henkjannl/RoomThermostat/05 Software/Roomthermostat V2/Roomthermostat V2.0/design/architecture.ods

# | File | Module | Functionality | Called by | V1 | V2 | V3 | V4 | V5 | V6 | Include list
a | constants |  | Global constants |  | basic | basic | basic | basic | basic | basic | #include "a_constants.h"
b | interfaces |  | Datatypes for interfaces between objects |  | basic | basic | basic | basic | basic | basic | #include "b_interfaces.h"
c | logger | Logger |  |  | none | none | none | none | none | none | #include "c_logger.h"
d | boiler | Boiler | Sends requested water temperature Requests boiler status | MenuUnit and MenuTelegram Main loop for boiler status Locking mechanism with Buttons | stub | stub | stub | stub | stub | stub | #include "d_boiler.h"
e | roomtemp | RoomTemp | Measures roomtemperature |  | stub | stub | stub | stub | stub | stub | #include "e_roomtemp.h"
f | telegram | Telegram | Telegram connection | Main loop | none | none | none | none | none | none | #include "f_telegram.h"
g | button | Buttons | Polls each of the 3 buttons | Timer interrupt Locking mechanism with OpenTherm | full | full | full | full | full | full | #include "g_button.h"
h | display | Display | Displays latest status of bolier and menu | MenuUnit and OpenTherm | stub | basic | basic | basic | basic | basic | #include "h_display.h"
i | jpeg | JPEG | Library to display images | Display | full | full | full | full | full | full | #include "i_jpeg.h"
j | storage | Storage | Stores and retrieves program from non volatile memory |  | none | none | none | none | none | none | #include "j_storage.h"
k | wifi | WiFi | WiFi connection | Main loop | stub | stub | stub | stub | stub | stub | #include "k_wifi.h"
l | time | Time | Real time clock | Main loop | stub | stub | stub | stub | stub | stub | #include "l_time.h"
m | menu_telegram | MenuTelegram | Manages menu state for each Telegram user | Telegram | none | none | none | none | none | none | #include "m_menu_telegram.h"
n | menu_unit | MenuUnit | Manages menu state for the hardware unit | Buttons | basic | basic | basic | basic | basic | basic | #include "n_menu_unit.h"
o | controller | Controller | Temperature controller including - thermostat program - PID controller for boiler temperature | Main loop | basic | basic | basic | basic | basic | basic | #include "o_controller.h"
