henkjannl/RoomThermostat/02 User interface/GUI.jpg

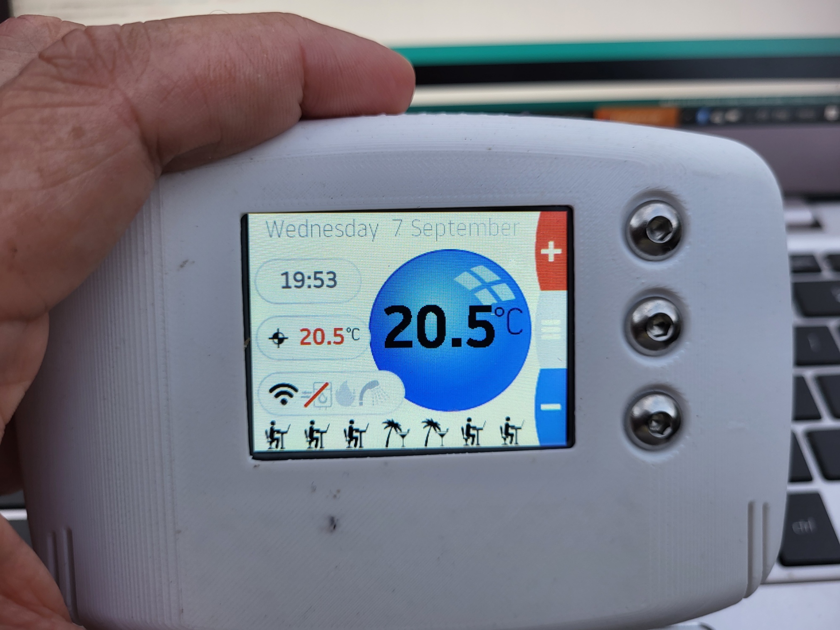
02 User interface/GUI.jpg
