henkjannl/RoomThermostat/02 User interface/photo.png

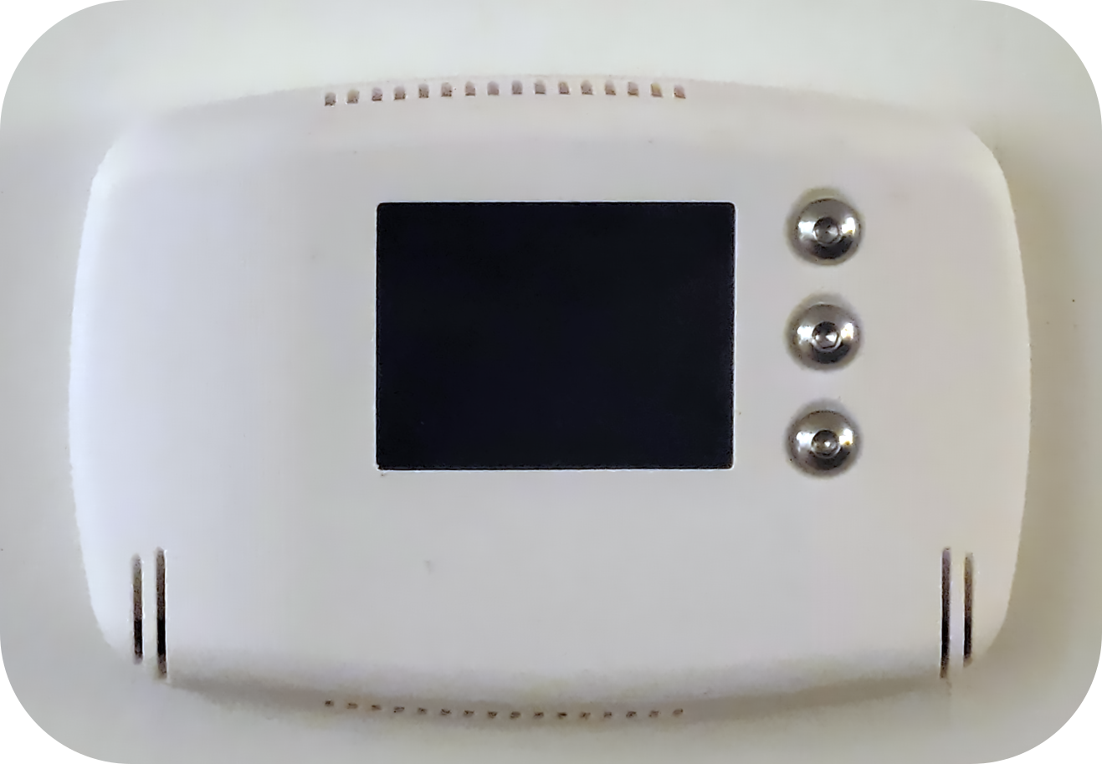
02 User interface/photo.png
