henkjannl/RoomThermostat/02 User interface/Telegram menu.png

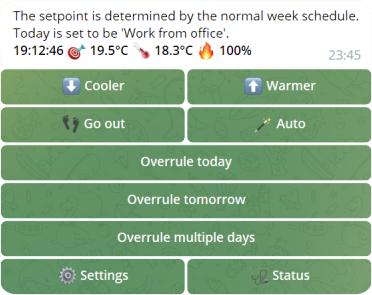
02 User interface/Telegram menu.png
