henkjannl/RoomThermostat/04 Electrical/Redesign PCB 3.0/20250117_201235.jpg

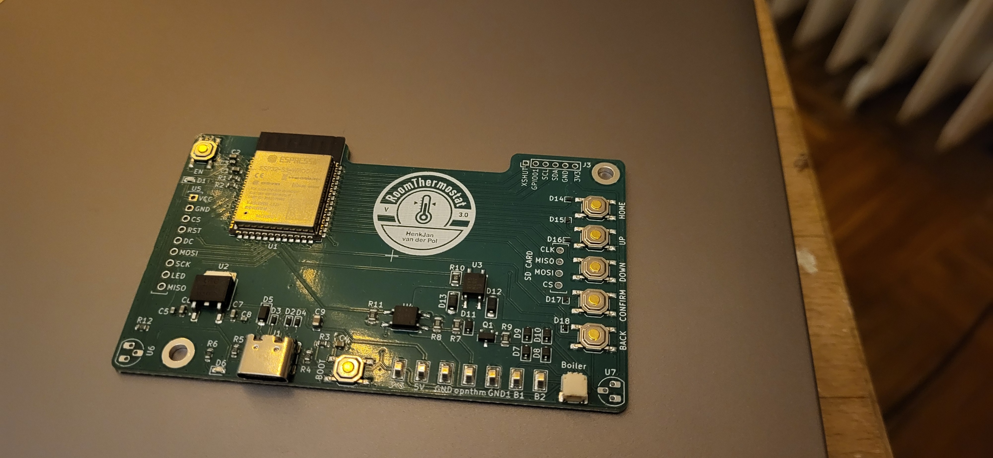
04 Electrical/Redesign PCB 3.0/20250117_201235.jpg
