henkjannl/RoomThermostat/04 Electrical/Redesign PCB 3.0/Interface board example project/Background info/Reverse engineering - case 4.png

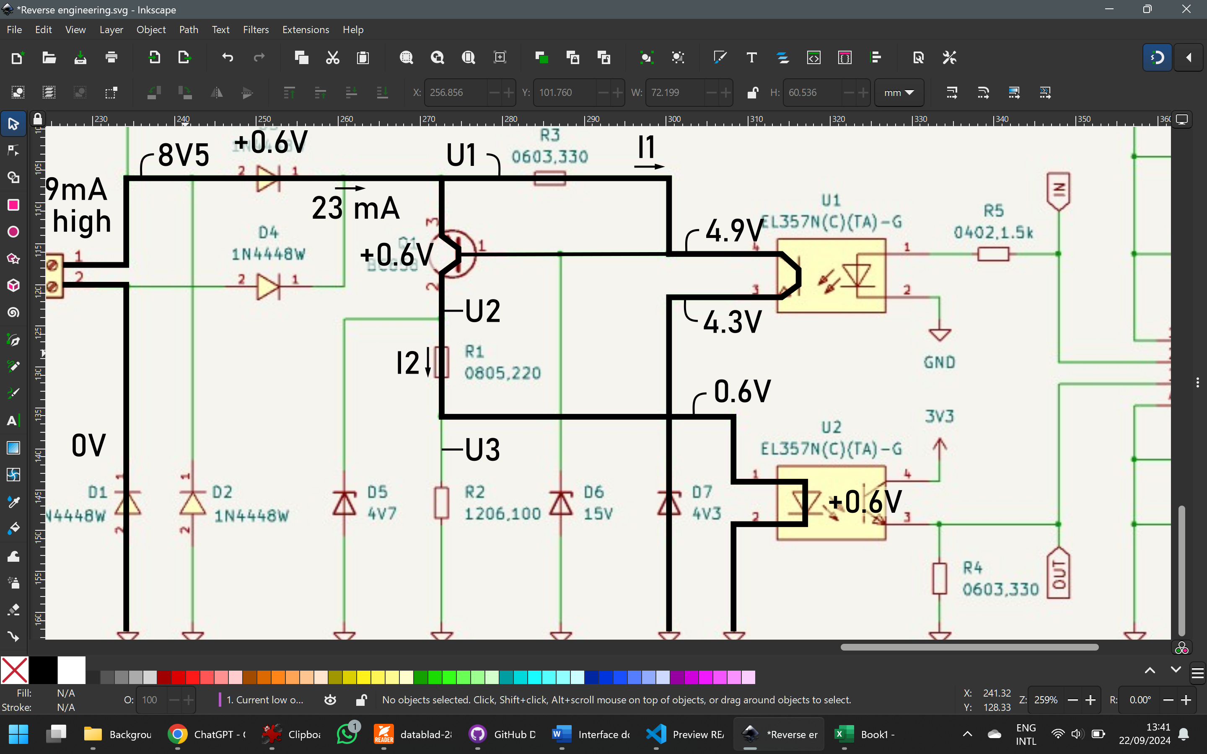
04 Electrical/Redesign PCB 3.0/Interface board example project/Background info/Reverse engineering - case 4.png
