henkjannl/RoomThermostat/04 Electrical/Redesign PCB 3.0/Photos DIYless/01.jpg

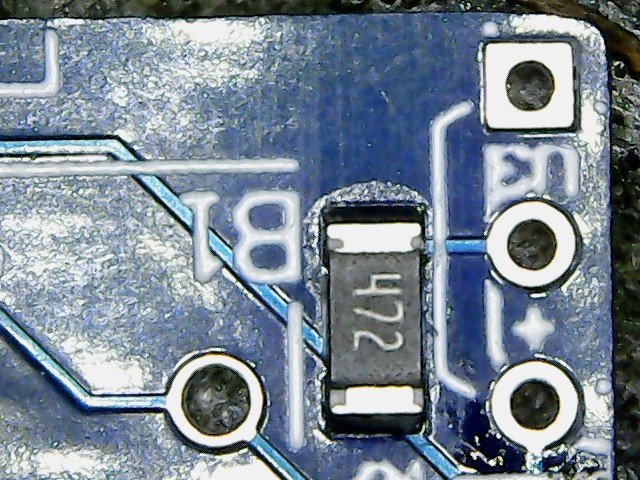
04 Electrical/Redesign PCB 3.0/Photos DIYless/01.jpg
