henkjannl/RoomThermostat/04 Electrical/Redesign PCB 3.0/Photos DIYless/09.jpg

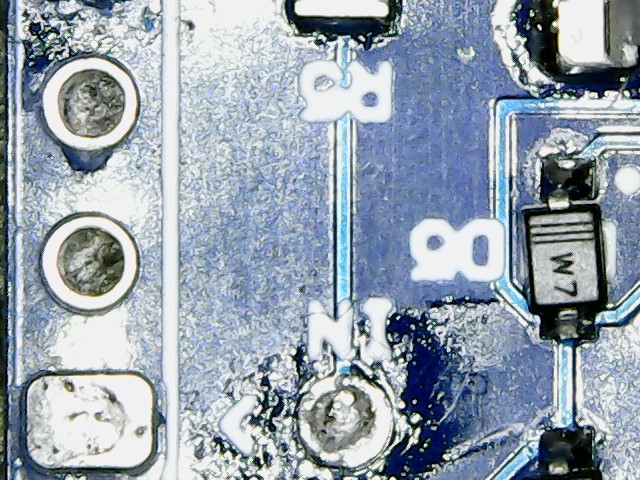
04 Electrical/Redesign PCB 3.0/Photos DIYless/09.jpg
