henkjannl/RoomThermostat/04 Electrical/Redesign PCB 3.0/Photos DIYless/17.jpg

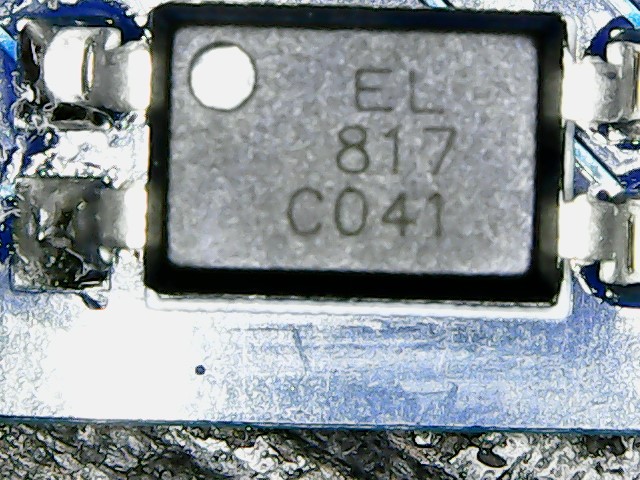
04 Electrical/Redesign PCB 3.0/Photos DIYless/17.jpg
