henkjannl/RoomThermostat/04 Electrical/Redesign PCB 3.0/Photos DIYless/18.jpg

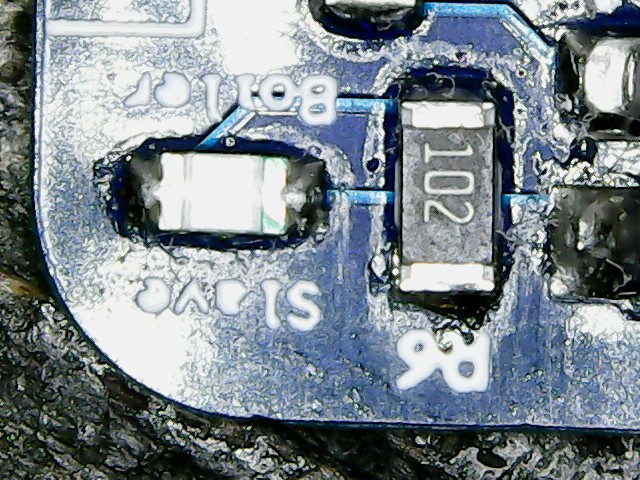
04 Electrical/Redesign PCB 3.0/Photos DIYless/18.jpg
