henkjannl/RoomThermostat/06 Logdata/Multiple day log.png

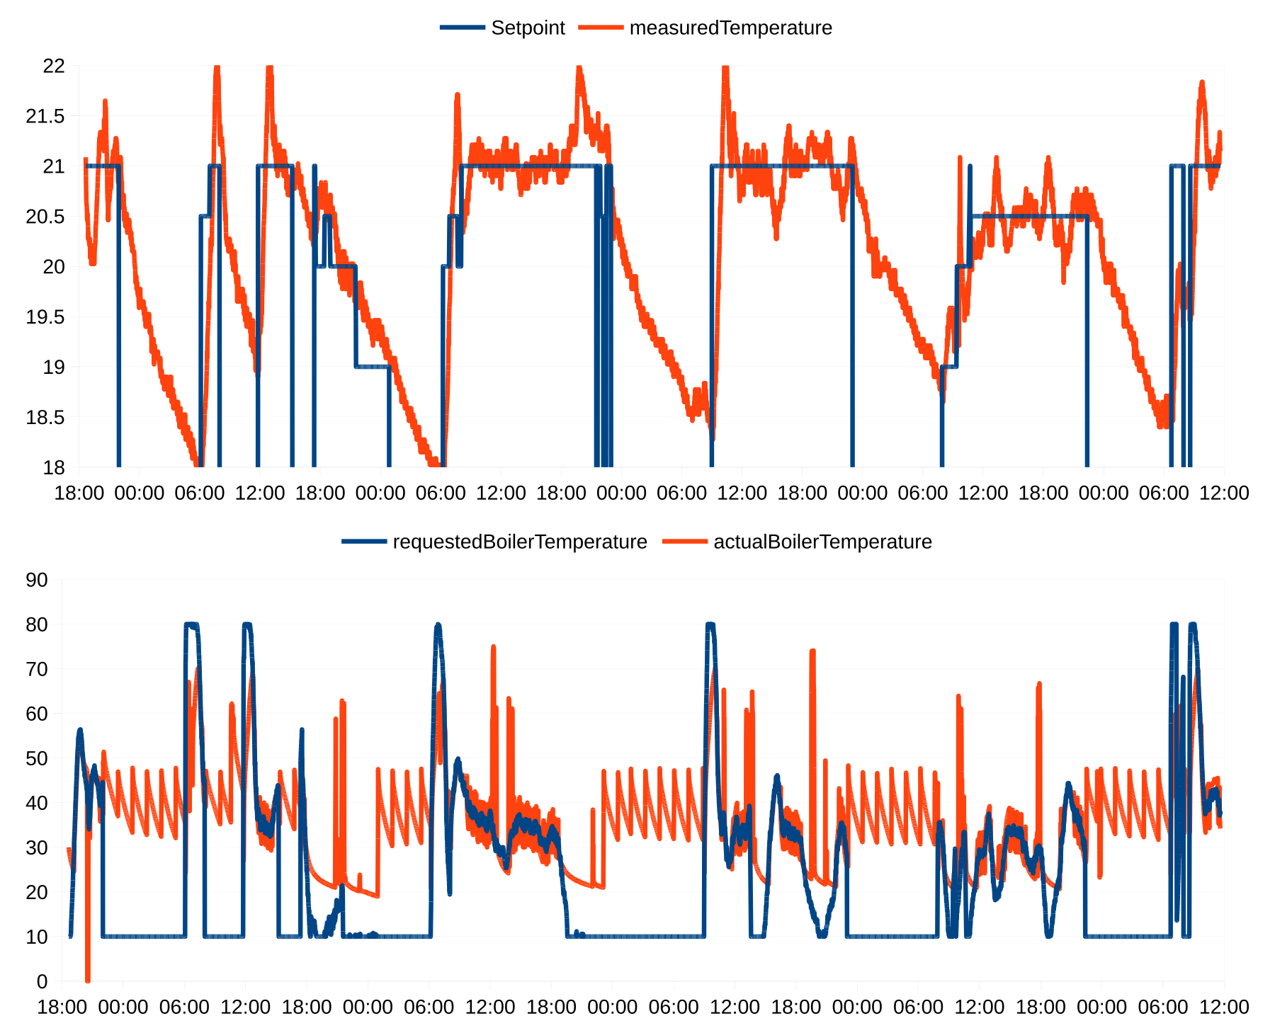
06 Logdata/Multiple day log.png
