henkjannl/RoomThermostat/07 Readonly/DIYless opentherm shield/Master Opentherm Shield 2.png

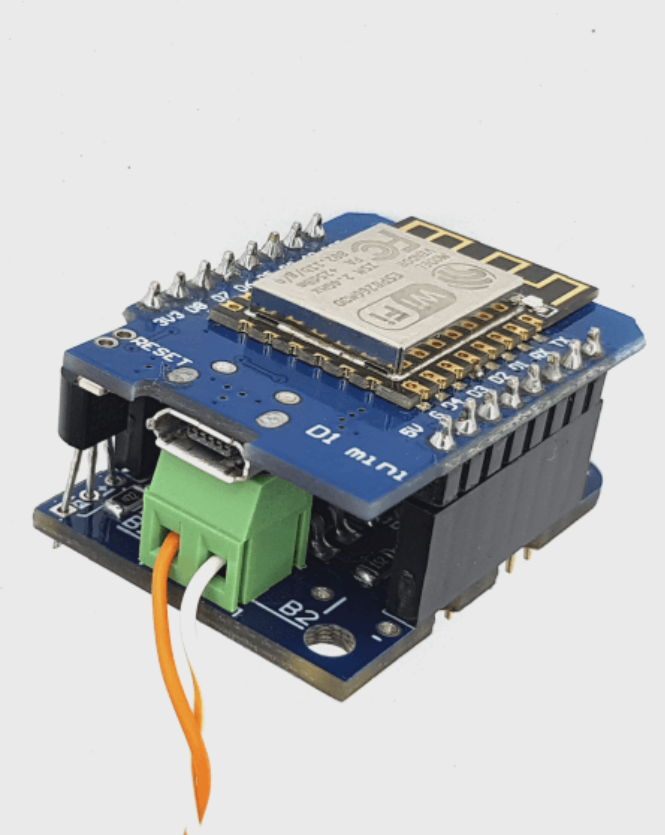
07 Readonly/DIYless opentherm shield/Master Opentherm Shield 2.png
