henkjannl/RoomThermostat/07 Readonly/DIYless opentherm shield/Master Opentherm Shield 3.png

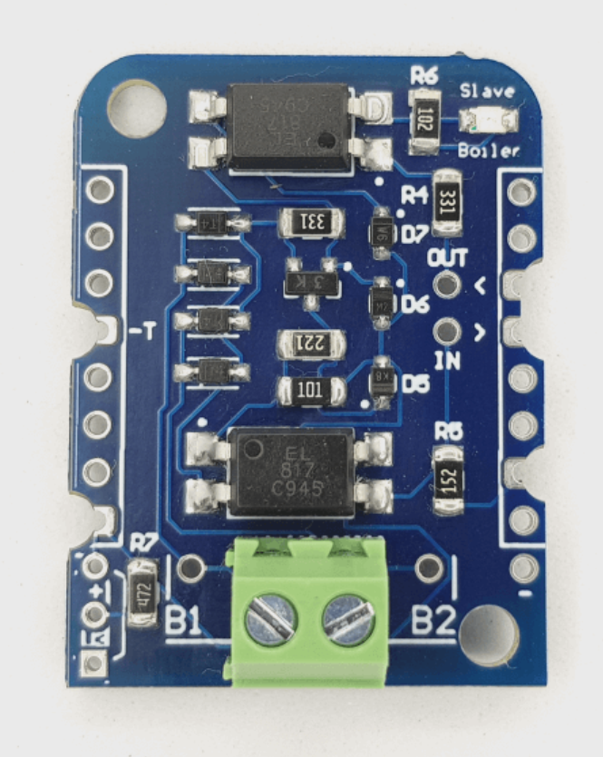
07 Readonly/DIYless opentherm shield/Master Opentherm Shield 3.png
