henkjannl/RoomThermostat/07 Readonly/DIYless opentherm shield/Master Opentherm Shield 4.png

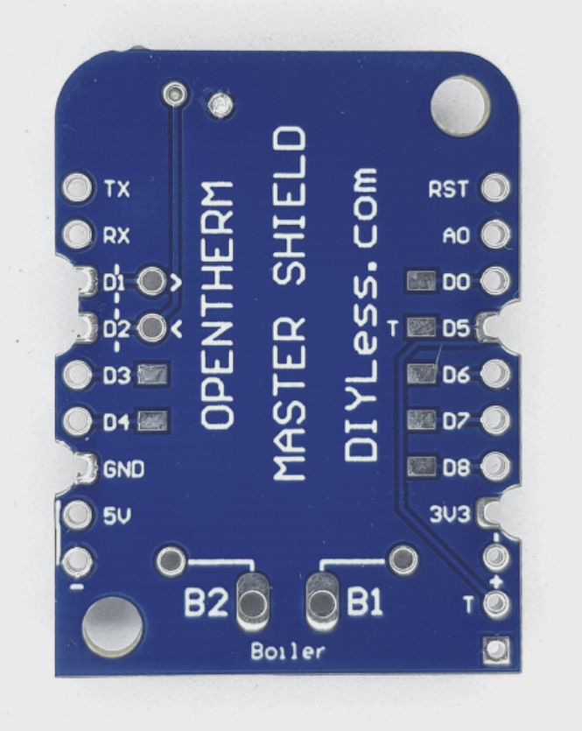
07 Readonly/DIYless opentherm shield/Master Opentherm Shield 4.png
