henkjannl/RoomThermostat/07 Readonly/DIYless opentherm shield/Schematic.png

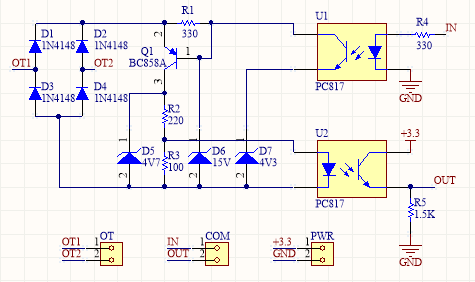
07 Readonly/DIYless opentherm shield/Schematic.png
