henkjannl/RoomThermostat/04 Electrical/Redesign PCB 3.0/Interface board example project/Background info/checklist.xlsx

Sheet: bom
New schematic | Original schematic | Original value | New value | LCSC Part # | Original description |  | Conrad Part No | Part subtype? | Current? | Orientation schematic? | Orientation board? | Footprint? | Datasheet | Footprint
D1 | D5 | 1N4148 | 1N4148WS_T4 | C2128 | Diode | Diode | 162280-89 |  |  |  |  |  | https://item.szlcsc.com/295156.html | SOD-323_L1.8-W1.3-LS2.5-RD
D2 | D6 | 1N4148 | 1N4148WS_T4 | C2128 | Diode | Diode | 162280-89 |  |  |  |  |  | https://item.szlcsc.com/295156.html | SOD-323_L1.8-W1.3-LS2.5-RD
D3 | D8 | 1N4148 | 1N4148WS_T4 | C2128 | Diode | Diode | 162280-89 |  |  |  |  |  | https://item.szlcsc.com/295156.html | SOD-323_L1.8-W1.3-LS2.5-RD
D4 | D7 | 1N4148 | 1N4148WS_T4 | C2128 | Diode | Diode | 162280-89 |  |  |  |  |  | https://item.szlcsc.com/295156.html | SOD-323_L1.8-W1.3-LS2.5-RD
D5 | D9 | 4V7 | 4V7 | C353517 | Zener Diode | Zener diode | 180084-89 |  |  |  |  |  | ~ | SOD-323_L1.8-W1.3-LS2.5-RD
D6 | D10 | 15V | 15V | C2104 | Zener Diode | Zener diode | 180203-89 |  |  |  |  |  | ~ | SOD-123_L2.7-W1.6-LS3.7-RD-1
D7 | D11 | 4V3 | 4V3 | C726993 | Zener Diode | Zener diode | 180076-89 |  |  |  |  |  | ~ | SOD-123_L2.7-W1.6-LS3.7-RD-1
J1 | - | - | Boiler | C395849 | Generic screw terminal, single row, 01x02, script generated (kicad-library-utils/schlib/autogen/connector/) |  | - |  |  |  |  |  | ~ | TerminalBlock_RND:TerminalBlock_RND_205-00001_1x02_P5.00mm_Horizontal
J2 | - | - | Screw_Terminal_01x04 | C557656 | Generic screw terminal, single row, 01x04, script generated (kicad-library-utils/schlib/autogen/connector/) |  | - |  |  |  |  |  | ~ | TerminalBlock_4Ucon:TerminalBlock_4Ucon_1x04_P3.50mm_Vertical
Q1 | Q1 | BC558A | BC858 | C549539 | PNP Transistor | PNP transistor, base/collector/emitter | 1262971-89 |  |  |  |  |  | ~ | SOT-23-5_L3.0-W1.7-P0.95-LS2.8-BL
R1 | R3 | 220 | 805220 | C17557 | 1/4 Watt 5% Resistor | 1% 1 8W Thick Film Resistors 150V 100ppm -55 155 220 0805 Chip Resistor - Surface Mount ROHS | 1417693-89 |  |  |  |  |  | https://datasheet.lcsc.com/lcsc/2110251830_UNI-ROYAL-Uniroyal-Elec-0805W8F2200T5E_C17557.pdf | 0805_2012Metric
R2 | R2 | 100 | 1206100 | C17901 | 1/4 Watt 5% Resistor |  | 1417639-89 |  |  |  |  |  |  | 1206_3216Metric
R3 | R1 | 330 | 603330 | C23138 | 1/4 Watt 5% Resistor | 1% 1 4W Thick Film Resistors 200V 100ppm -55 155 100 1206 Chip Resistor - Surface Mount ROHS | 1417730-89 |  |  |  |  |  | https://datasheet.lcsc.com/lcsc/2110252130_UNI-ROYAL-Uniroyal-Elec-0603WAF3300T5E_C23138.pdf | 0603_1608Metric
R4 | R4 | 330 | 603330 | C23138 | 1/4 Watt 5% Resistor | 1% 1 10W Thick Film Resistors 75V 100ppm -55 155 330 0603 Chip Resistor - Surface Mount ROHS | 1417730-89 |  |  |  |  |  | https://datasheet.lcsc.com/lcsc/2110252130_UNI-ROYAL-Uniroyal-Elec-0603WAF3300T5E_C23138.pdf | 0603_1608Metric
R5 | R8 | 1k2 | 0402,1.5k | C25867 | 1/4 Watt 5% Resistor | 1% 1 10W Thick Film Resistors 75V 100ppm -55 155 330 0603 Chip Resistor - Surface Mount ROHS | 1417712-89 |  |  |  |  |  |  | 0402_1005Metric
U1 | OK1A | PC827 | EL357N(C)(TA)-G | C29981 | Dual opto-coupler |  | 140235-89 |  |  |  |  |  | https://item.szlcsc.com/7114.html | OPTO-SMD-4_L4.4-W4.1-P2.54-LS7.0-TL
U2 | OK1B | PC827 | EL357N(C)(TA)-G | C29981 | Dual opto-coupler |  | 140235-89 |  |  |  |  |  | https://item.szlcsc.com/7114.html | OPTO-SMD-4_L4.4-W4.1-P2.54-LS7.0-TL
D5 |  |  | 4V7 |  |  |  |  |  |  |  |  |  | ~ | footprint:SOD-323_L1.8-W1.3-LS2.5-RD
D6 |  |  | 15V |  |  |  |  |  |  |  |  |  | ~ | footprint:SOD-123_L2.7-W1.6-LS3.7-RD-1
D7 |  |  | 4V3 |  |  |  |  |  |  |  |  |  | ~ | footprint:SOD-123_L2.7-W1.6-LS3.7-RD-1
J1 |  |  | Boiler
J2 |  |  | Screw_Terminal_01x04
Q1 |  |  | BC858 |  |  |  |  |  |  |  |  |  | ~ | footprint:SOT-23-3_L2.9-W1.3-P1.90-LS2.4-BR
R1 |  |  | 805220 |  |  |  |  |  |  |  |  |  | https://datasheet.lcsc.com/lcsc/2110251830_UNI-ROYAL-Uniroyal-Elec-0805W8F2200T5E_C17557.pdf | footprint:0805_2012Metric
R2 |  |  | 1206100 |  |  |  |  |  |  |  |  |  | https://datasheet.lcsc.com/lcsc/2110251930_UNI-ROYAL-Uniroyal-Elec-1206W4F1000T5E_C17901.pdf | footprint:1206_3216Metric
R3,R4 |  |  | 603330 |  |  |  |  |  |  |  |  |  | https://datasheet.lcsc.com/lcsc/2110252130_UNI-ROYAL-Uniroyal-Elec-0603WAF3300T5E_C23138.pdf | footprint:0603_1608Metric
R5 |  |  | 0402,1.5k |  |  | 1% 1 16W Thick Film Resistors 50V 100ppm -55 155 1 5k 0402 Chip Resistor - Surface Mount ROHS |  |  |  |  |  |  | https://datasheet.lcsc.com/lcsc/2110260030_UNI-ROYAL-Uniroyal-Elec-0402WGF1501TCE_C25867.pdf | footprint:0402_1005Metric
U1,U2 |  |  | EL357N(C)(TA)-G |  |  |  |  |  |  |  |  |  |  | footprint:OPTO-SMD-4_L4.4-W4.1-P2.54-LS7.0-TL

Sheet: Sheet1
Qty | Description | Value | Reference | Conrad Part No
1 | PIC processor | PIC16F88P | IC1 | 165233-89
1 | RS232 interfacemodule | MAX232 | IC2 | 152281-89
1 | Voltage Regulator TO220 | MC7805CT | IC3 | 175030-89
1 | Dual opto-coupler | PC827 | OK1 | 140235-89
4 | PNP Transistor | BC558A | Q1, Q2, Q3, Q5 | 1262971-89
1 | NPN Transistor | BC547B | Q4 | 1262957-89
1 | Electrolytic Capacitor, Radial 63V | 220µF | C1 | 445902-89
1 | Electrolytic Capacitor, Radial 16V | 100µF | C2 | 445928-89
4 | Electrolytic Capacitor, Radial 50V | 1µF | C3, C4, C5, C6 | 445724-89
4 | Diode | 1N4004 | D1, D2, D3, D4 | 162248-89
4 | Diode | 1N4148 | D5, D6, D7, D8 | 162280-89
1 | Zener Diode | 4V7 | D9 | 180084-89
1 | Zener Diode | 15V | D10 | 180203-89
1 | Zener Diode | 4V3 | D11 | 180076-89
1 | 1/4 Watt 5% Resistor | 39 | R12 | 1417702-89
2 | 1/4 Watt 5% Resistor | 100 | R2, R11 | 1417639-89
1 | 1/4 Watt 5% Resistor | 220 | R3 | 1417693-89
2 | 1/4 Watt 5% Resistor | 330 | R1, R4 | 1417730-89
1 | 1/4 Watt 5% Resistor | 1k2 | R8 | 1417712-89 | 1k2 or 1k5?
2 | 1/4 Watt 5% Resistor | 4k7 | R6, R9 | 1417695-89
1 | 1/4 Watt 5% Resistor | 15k | R10 | 1417711-89
2 | 1/4 Watt 5% Resistor | 33k | R5, R7 | 1417647-89
1* | Transformer EI30 | 15V 1.2VA | TR1 | 710691-89
1 | Header | 10 pin | SV1 | 741648-89
3 | Screw Clamp | 2 pin | X1, X2, X3 | 731091-89

Sheet: NewKicadProject
Reference | Value | LCSC | Datasheet | Footprint | Qty | DNP | Description
D1,D2,D3,D4 | 1N4148WS_T4 | C2128 | https://item.szlcsc.com/295156.html | footprint:SOD-323_L1.8-W1.3-LS2.5-RD | 4
D5 | 4V7 | C353517 | ~ | footprint:SOD-323_L1.8-W1.3-LS2.5-RD | 1 |  | Zener diode
D6 | 15V | C2104 | ~ | footprint:SOD-123_L2.7-W1.6-LS3.7-RD-1 | 1 |  | Zener diode
D7 | 4V3 | C726993 | ~ | footprint:SOD-123_L2.7-W1.6-LS3.7-RD-1 | 1 |  | Zener diode
J1 | Boiler | C395849 | ~ | TerminalBlock_RND:TerminalBlock_RND_205-00001_1x02_P5.00mm_Horizontal | 1 |  | Generic screw terminal, single row, 01x02, script generated (kicad-library-utils/schlib/autogen/connector/)
J2 | Screw_Terminal_01x04 | C557656 | ~ | TerminalBlock_4Ucon:TerminalBlock_4Ucon_1x04_P3.50mm_Vertical | 1 |  | Generic screw terminal, single row, 01x04, script generated (kicad-library-utils/schlib/autogen/connector/)
Q1 | BC858 | C549539 | ~ | footprint:SOT-23-3_L2.9-W1.3-P1.90-LS2.4-BR | 1 |  | PNP transistor, base/collector/emitter
R1 | 805220 | C17557 | https://datasheet.lcsc.com/lcsc/2110251830_UNI-ROYAL-Uniroyal-Elec-0805W8F2200T5E_C17557.pdf | footprint:0805_2012Metric | 1 |  | 1% 1 8W Thick Film Resistors 150V 100ppm -55 155 220 0805 Chip Resistor - Surface Mount ROHS
R2,R3 | 603330 | C23138 | https://datasheet.lcsc.com/lcsc/2110252130_UNI-ROYAL-Uniroyal-Elec-0603WAF3300T5E_C23138.pdf | footprint:0603_1608Metric | 2 |  | 1% 1 10W Thick Film Resistors 75V 100ppm -55 155 330 0603 Chip Resistor - Surface Mount ROHS
R4 | 0402,1.5k | C25867 | https://datasheet.lcsc.com/lcsc/2110260030_UNI-ROYAL-Uniroyal-Elec-0402WGF1501TCE_C25867.pdf | footprint:0402_1005Metric | 1 |  | 1% 1 16W Thick Film Resistors 50V 100ppm -55 155 1 5k 0402 Chip Resistor - Surface Mount ROHS
R6 | 1206100 | C17901 | https://datasheet.lcsc.com/lcsc/2110251930_UNI-ROYAL-Uniroyal-Elec-1206W4F1000T5E_C17901.pdf | footprint:1206_3216Metric | 1 |  | 1% 1 4W Thick Film Resistors 200V 100ppm -55 155 100 1206 Chip Resistor - Surface Mount ROHS
U1,U2 | EL357N(C)(TA)-G | C29981 | https://item.szlcsc.com/7114.html | footprint:OPTO-SMD-4_L4.4-W4.1-P2.54-LS7.0-TL | 2
