henkjannl/RoomThermostat/05 Software/Tests/Test08_monitor_chromoterm/Monitoring the Honeywell.xlsx

Sheet: Sheet1
Max voltage | U1 | 18 | V |  | R2 |  | R1 | U2 | I | 2.668769716
Scaled down to | U2 | 2.4 | V |  | 10
 |  |  |  |  | 22
U2/R1=U1/(R1+R2) |  |  |  |  | 47
U2*R1+U2*R2=U1*R1 |  |  |  |  | 100 | 17.64705882 | 10 | 1.636363636 | 0.1636363636
(U2-U1)*R1=-U2*R2 |  |  |  |  | 150 | 26.47058824 | 22 | 2.302325581 | 0.1046511628
R2=(U1-U2)/U2*R1 |  |  |  |  | 200 | 35.29411765 | 22 | 1.783783784 | 0.08108108108
 |  |  |  |  | 220 | 38.82352941 | 22 | 1.636363636 | 0.07438016529
Resistor 1 | R1 | 330 | ohm |  | 270 | 47.64705882 | 47 | 2.668769716 | 0.05678233438
Resistor 2 | R2 | 2000 | ohm |  | 330 | 58.23529412 | 47 | 2.24403183 | 0.04774535809
 |  |  |  |  | 470 | 82.94117647 | 47 | 1.636363636 | 0.03481624758
 |  | U1 | U2 | readout | 510 | 90 | 47 | 1.518850987 | 0.03231597846
 |  | 18 | 2.549356223 | 3163.519313 | 680 | 120 | 100 | 2.307692308 | 0.02307692308
 |  | 16.9 | 2.393562232 | 2970.193133 | 1000 | 176.4705882 | 150 | 2.347826087 | 0.01565217391
 |  | 8.9 | 1.260515021 | 1564.184549 | 2000 | 352.9411765 | 330 | 2.549356223 | 0.007725321888
 |  | 6.3 | 0.8922746781 | 1107.23176 | 2200 | 388.2352941 | 330 | 2.347826087 | 0.007114624506
 |  | 0 | 0 | 0 | 3300 | 582.3529412 | 510 | 2.409448819 | 0.004724409449
 |  |  |  |  | 4700 | 829.4117647 | 680 | 2.275092937 | 0.003345724907
Readout scale |  | 0.00568986569 |  |  | 5100 | 900 | 680 | 2.117647059 | 0.003114186851
 |  |  |  |  | 6800 | 1200 | 1000 | 2.307692308 | 0.002307692308
 |  |  |  |  | 10000 | 1764.705882 | 1000 | 1.636363636 | 0.001636363636
 |  |  |  |  | 20000 | 3529.411765 | 3300 | 2.549356223 | 0.0007725321888
 |  |  |  |  | 47000 | 8294.117647 | 6800 | 2.275092937 | 0.0003345724907
 |  |  |  |  | 51000 | 9000 | 6800 | 2.117647059 | 0.0003114186851
 |  |  |  |  | 68000 | 12000 | 10000 | 2.307692308 | 0.0002307692308
 |  |  |  |  | 100000 | 17647.05882 | 10000 | 1.636363636 | 0.0001636363636
 |  |  |  |  | 220000 | 38823.52941 | 20000 | 1.5 | 7.5e-05
 |  |  |  |  | 300000 | 52941.17647 | 51000 | 2.615384615 | 5.128205128e-05
 |  |  |  |  | 470000 | 82941.17647 | 68000 | 2.275092937 | 3.345724907e-05
 |  |  |  |  | 680000 | 120000 | 100000 | 2.307692308 | 2.307692308e-05
 |  |  |  |  | 1000000 | 176470.5882 | 100000 | 1.636363636 | 1.636363636e-05

Sheet: Sheet2
217 | 4490
46
218
43
220
43
228
44
230
35
230
34
233
36
235
34
235
32
231
30
235
35
240
31
240
31
240
33
240
31
240
240

Sheet: Sheet3
Utotal | 18 | V
R2 | 2000 | ohm
R1 | 330 | ohm
Rtotal | 2330 | ohm
Itotal | 0.007725321888 | A
U1 | 2.549356223 | V
8.8
24.2
16.5
