henkjannl/RoomThermostat/04 Electrical/Redesign PCB 3.0/Interface board example project/Background info/Reverse engineering.xlsx

Sheet: Case 1
Case 1
Output | LOW
I1 | 0.009 | A
Value of U2 based on output
D6 | 15 | V
D7 | 4.3 | V
U2 | 15 | V
 |  |  |  |  |  |  | I2/I1 | U1 | U2 | U1-U2 | U3 | U4 | I4
Split I2/I3 |  |  |  |  |  |  |  | 15.0297 | 15 | 0.0297 | 4.7 | 1.46875 | 0.0146875
I2/I1 | 1% |  | I2+I3=I1 |  |  |  | 0% | 15 | 15 | 0 | 4.7 | 1.46875 | 0.0146875
I2 | 9e-05 | A | I2/I3=p |  |  |  | 5% | 15.1485 | 15 | 0.1485 | 4.7 | 1.46875 | 0.0146875
I3 | 0.00891 | A | I2=p*I3 |  |  |  | 10% | 15.297 | 15 | 0.297 | 4.7 | 1.46875 | 0.0146875
R3 | 330 | Ω | I2+I2/p=I1 |  |  |  | 15% | 15.4455 | 15 | 0.4455 | 4.7 | 1.46875 | 0.0146875
U1 | 15.0297 | V | I2=p*I1/(1+p) |  |  |  | 20% | 15.594 | 15 | 0.594 | 4.7 | 1.46875 | 0.0146875
 |  |  |  |  |  |  | 25% | 15.7425 | 15 | 0.7425 | 4.7 | 1.46875 | 0.0146875
U1-U2 | 0.0297 | V |  |  |  |  | 30% | 15.891 | 15 | 0.891 | 4.7 | 1.46875 | 0.0146875
Q1 will isolate |  |  |  |  |  |  | 35% | 16.0395 | 15 | 1.0395 | 4.7 | 1.46875 | 0.0146875
 |  |  |  |  |  |  | 40% | 16.188 | 15 | 1.188 | 4.7 | 1.46875 | 0.0146875
U3' | 14.4297 | V | Ignoring D5 |  |  |  | 45% | 16.3365 | 15 | 1.3365 | 4.7 | 1.46875 | 0.0146875
D5 | 4.7 | V |  |  |  |  | 50% | 16.485 | 15 | 1.485 | 4.7 | 1.46875 | 0.0146875
D5 will limit U3 |  |  |  |  |  |  | 55% | 16.6335 | 15 | 1.6335 | 4.7 | 1.46875 | 0.0146875
U3 | 4.7 | V |  |  |  |  | 60% | 16.782 | 15 | 1.782 | 4.7 | 1.46875 | 0.0146875
 |  |  |  |  |  |  | 65% | 16.9305 | 15 | 1.9305 | 4.7 | 1.46875 | 0.0146875
Ignoring Optocoupler: |  |  |  |  |  |  | 70% | 17.079 | 15 | 2.079 | 4.7 | 1.46875 | 0.0146875
R1 | 220 | Ω |  |  |  |  | 75% | 17.2275 | 15 | 2.2275 | 4.7 | 1.46875 | 0.0146875
R2 | 100 | Ω |  | U4 | 1.3 | V | 80% | 17.376 | 15 | 2.376 | 4.7 | 1.46875 | 0.0146875
I4 | 0.0146875 | A |  |  |  |  | 85% | 17.5245 | 15 | 2.5245 | 4.7 | 1.46875 | 0.0146875
U4 | 1.46875 | V |  |  |  |  | 90% | 17.673 | 15 | 2.673 | 4.7 | 1.46875 | 0.0146875
 |  |  |  |  |  |  | 95% | 17.8215 | 15 | 2.8215 | 4.7 | 1.46875 | 0.0146875
Opamp will limit U4 |  |  |  |  |  |  | 100% | 17.97 | 15 | 2.97 | 4.7 | 1.46875 | 0.0146875
U4 | 1.3 | V
I4 | 0.01545454545 | A |  |  |  |  | Average | 16.485 | 15 |  | 4.7 | 1.46875 | 0.0146875
I5 | -0.006544545455 | A
Recalculate I4 if I5<0
I4 | 0.00891 | A
U3 | 3.2602 | V
U1-U3 | 11.7695 | V

Sheet: Case 2
Case 2
Output | HIGH
I1 | 0.009 | A
Value of U2 based on output
D6 | 15 | V
D7 | 4.3 | V
U2 | 4.3 | V
 |  |  |  |  |  |  | I2/I1 | U1 | U2 | U3 | U4 | I4
Split I2/I3 |  |  |  |  |  |  |  | 4.3 | 3.7 | 3.28 | 1.3 | 0.0115625
I2/I1 | 0% |  | I2+I3=I1 |  |  |  | 0% | 4.3 | 3.7 | 3.28 | 1.3 | 0.0115625
I2 | 0 | A | I2/I3=p |  |  |  | 5% | 4.4485 | 3.8485 | 3.181 | 1.3 | 0.0120265625
I3 | 0.009 | A | I2=p*I3 |  |  |  | 10% | 4.597 | 3.997 | 3.082 | 1.3 | 0.012490625
R3 | 330 | Ω | I2=I1/(1+p) |  |  |  | 15% | 4.7455 | 4.1455 | 2.983 | 1.3 | 0.0129546875
U1 | 4.3 | V |  |  |  |  | 20% | 4.894 | 4.294 | 2.884 | 1.3 | 0.01341875
 |  |  |  |  |  |  | 25% | 5.0425 | 4.4425 | 2.785 | 1.3 | 0.0138828125
U1-U2 | 0 | V |  |  |  |  | 30% | 5.191 | 4.591 | 2.686 | 1.3 | 0.014346875
Q1 will isolate |  |  |  |  |  |  | 35% | 5.3395 | 4.7 | 2.587 | 1.3 | 0.0146875
 |  |  |  |  |  |  | 40% | 5.488 | 4.7 | 2.488 | 1.3 | 0.0146875
U3' | 3.7 | V | Ignoring D5 |  |  |  | 45% | 5.6365 | 4.7 | 2.389 | 1.3 | 0.0146875
D5 | 4.7 | V |  |  |  |  | 50% | 5.785 | 4.7 | 2.29 | 1.3 | 0.0146875
D5 will not limit U3 |  |  |  |  |  |  | 55% | 5.9335 | 4.7 | 2.191 | 1.3 | 0.0146875
U3 | 3.7 | V |  |  |  |  | 60% | 6.082 | 4.7 | 2.092 | 1.3 | 0.0146875
 |  |  |  |  |  |  | 65% | 6.2305 | 4.7 | 1.993 | 1.3 | 0.0146875
Ignoring Optocoupler: |  |  |  |  |  |  | 70% | 6.379 | 4.7 | 1.894 | 1.3 | 0.0146875
R1 | 220 | Ω |  |  |  |  | 75% | 6.5275 | 4.7 | 1.795 | 1.3 | 0.0146875
R2 | 100 | Ω |  | U4 | 1.3 | V | 80% | 6.676 | 4.7 | 1.696 | 1.3 | 0.0146875
I4 | 0.0115625 | A |  |  |  |  | 85% | 6.8245 | 4.7 | 1.597 | 1.3 | 0.0146875
U4 | 1.15625 | V |  |  |  |  | 90% | 6.973 | 4.7 | 1.498 | 1.3 | 0.0146875
 |  |  |  |  |  |  | 95% | 7.1215 | 4.7 | 1.399 | 1.3 | 0.0146875
Opamp will limit U4 |  |  |  |  |  |  | 100% | 7.27 | 4.7 | 1.3 | 1.3 | 0.0146875
U4 | 1.3 | V
I4 | 0.01090909091 | A
I5 | -0.001909090909 | A
Recalculate I4 if I5<0
I4 | 0.009 | A
U3 | 3.28 | V
U1-U3 | 1.02 | V

Sheet: Case 3
Case 3
Output | LOW
I1 | 0.023 | A
Value of U2 based on output
D6 | 15 | V
D7 | 4.3 | V
U2 | 15 | V
 |  |  |  |  |  |  | I2/I1 | U1 | U2 | U3 | U4 | I4
Split I2/I3 |  |  |  |  |  |  |  | 15 | 4.7 | 4.7 | 1.3 | 0.0146875
I2/I1 | 0% |  | I2+I3=I1 |  |  |  | 0% | 15 | 4.7 | 4.7 | 1.3 | 0.0146875
I2 | 0 | A | I2/I3=p |  |  |  | 5% | 15.3795 | 4.7 | 4.7 | 1.3 | 0.0146875
I3 | 0.023 | A | I2=p*I3 |  |  |  | 10% | 15.759 | 4.7 | 4.7 | 1.3 | 0.0146875
R3 | 330 | Ω | I2=I1/(1+p) |  |  |  | 15% | 16.1385 | 4.7 | 4.7 | 1.3 | 0.0146875
U1 | 15 | V |  |  |  |  | 20% | 16.518 | 4.7 | 4.7 | 1.3 | 0.0146875
 |  |  |  |  |  |  | 25% | 16.8975 | 4.7 | 4.7 | 1.3 | 0.0146875
U1-U2 | 0 | V |  |  |  |  | 30% | 17.277 | 4.7 | 4.7 | 1.3 | 0.0146875
Q1 will isolate |  |  |  |  |  |  | 35% | 17.6565 | 4.7 | 4.589 | 1.3 | 0.0146875
 |  |  |  |  |  |  | 40% | 18.036 | 4.7 | 4.336 | 1.3 | 0.0146875
U3' | 14.4 | V | Ignoring D5 |  |  |  | 45% | 18.4155 | 4.7 | 4.083 | 1.3 | 0.0146875
D5 | 4.7 | V |  |  |  |  | 50% | 18.795 | 4.7 | 3.83 | 1.3 | 0.0146875
D5 will limit U3 |  |  |  |  |  |  | 55% | 19.1745 | 4.7 | 3.577 | 1.3 | 0.0146875
U3 | 4.7 | V |  |  |  |  | 60% | 19.554 | 4.7 | 3.324 | 1.3 | 0.0146875
 |  |  |  |  |  |  | 65% | 19.9335 | 4.7 | 3.071 | 1.3 | 0.0146875
Ignoring Optocoupler: |  |  |  |  |  |  | 70% | 20.313 | 4.7 | 2.818 | 1.3 | 0.0146875
R1 | 220 | Ω |  |  |  |  | 75% | 20.6925 | 4.7 | 2.565 | 1.3 | 0.0146875
R2 | 100 | Ω |  | U4 | 1.3 | V | 80% | 21.072 | 4.7 | 2.312 | 1.3 | 0.0146875
I4 | 0.0146875 | A |  |  |  |  | 85% | 21.4515 | 4.7 | 2.059 | 1.3 | 0.0146875
U4 | 1.46875 | V |  |  |  |  | 90% | 21.831 | 4.7 | 1.806 | 1.3 | 0.0146875
 |  |  |  |  |  |  | 95% | 22.2105 | 4.7 | 1.553 | 1.3 | 0.0146875
Opamp will limit U4 |  |  |  |  |  |  | 100% | 22.59 | 4.7 | 1.3 | 1.3 | 0.0146875
U4 | 1.3 | V
I4 | 0.01545454545 | A
I5 | 0.007545454545 | A
Recalculate I4 if I5<0
I4 | 0.01545454545 | A
U3 | 4.7 | V
U1-U3 | 10.3 | V

Sheet: Case 4
Case 2
Output | HIGH
I1 | 0.023 | A
Value of U2 based on output
D6 | 15 | V
D7 | 4.3 | V
U2 | 4.3 | V
 |  |  |  |  |  |  | I2/I1 | U1 | U2 | U3 | U4 | I4
Split I2/I3 |  |  |  |  |  |  |  | 4.3 | 3.7 | 3.7 | 1.3 | 0.0115625
I2/I1 | 0% |  | I2+I3=I1 |  |  |  | 0% | 4.3 | 3.7 | 3.7 | 1.3 | 0.0115625
I2 | 0 | A | I2/I3=p |  |  |  | 5% | 4.6795 | 4.0795 | 4.0795 | 1.3 | 0.0127484375
I3 | 0.023 | A | I2=p*I3 |  |  |  | 10% | 5.059 | 4.459 | 4.459 | 1.3 | 0.013934375
R3 | 330 | Ω | I2=I1/(1+p) |  |  |  | 15% | 5.4385 | 4.7 | 4.7 | 1.3 | 0.0146875
U1 | 4.3 | V |  |  |  |  | 20% | 5.818 | 4.7 | 4.7 | 1.3 | 0.0146875
 |  |  |  |  |  |  | 25% | 6.1975 | 4.7 | 4.7 | 1.3 | 0.0146875
U1-U2 | 0 | V |  |  |  |  | 30% | 6.577 | 4.7 | 4.7 | 1.3 | 0.0146875
Q1 will isolate |  |  |  |  |  |  | 35% | 6.9565 | 4.7 | 4.589 | 1.3 | 0.0146875
 |  |  |  |  |  |  | 40% | 7.336 | 4.7 | 4.336 | 1.3 | 0.0146875
U3' | 3.7 | V | Ignoring D5 |  |  |  | 45% | 7.7155 | 4.7 | 4.083 | 1.3 | 0.0146875
D5 | 4.7 | V |  |  |  |  | 50% | 8.095 | 4.7 | 3.83 | 1.3 | 0.0146875
D5 will not limit U3 |  |  |  |  |  |  | 55% | 8.4745 | 4.7 | 3.577 | 1.3 | 0.0146875
U3 | 3.7 | V |  |  |  |  | 60% | 8.854 | 4.7 | 3.324 | 1.3 | 0.0146875
 |  |  |  |  |  |  | 65% | 9.2335 | 4.7 | 3.071 | 1.3 | 0.0146875
Ignoring Optocoupler: |  |  |  |  |  |  | 70% | 9.613 | 4.7 | 2.818 | 1.3 | 0.0146875
R1 | 220 | Ω |  |  |  |  | 75% | 9.9925 | 4.7 | 2.565 | 1.3 | 0.0146875
R2 | 100 | Ω |  | U4 | 1.3 | V | 80% | 10.372 | 4.7 | 2.312 | 1.3 | 0.0146875
I4 | 0.0115625 | A |  |  |  |  | 85% | 10.7515 | 4.7 | 2.059 | 1.3 | 0.0146875
U4 | 1.15625 | V |  |  |  |  | 90% | 11.131 | 4.7 | 1.806 | 1.3 | 0.0146875
 |  |  |  |  |  |  | 95% | 11.5105 | 4.7 | 1.553 | 1.3 | 0.0146875
Opamp will limit U4 |  |  |  |  |  |  | 100% | 11.89 | 4.7 | 1.3 | 1.3 | 0.0146875
U4 | 1.3 | V
I4 | 0.01090909091 | A
I5 | 0.01209090909 | A
Recalculate I4 if I5<0
I4 | 0.01090909091 | A
U3 | 3.7 | V
U1-U3 | 0.6 | V

Sheet: Conclusion
Output | LOW | HIGH | LOW | HIGH
I1 | 0.009 | 0.009 | 0.023 | 0.023
U1 | 16.485 | 5.785 | 18.795 | 8.095
U3 | 4.7 | 2.29 | 2.29 | 2.29
U4 | 1.46875 | 1.3 | 1.3 | 1.3
