henkjannl/RoomThermostat/04 Electrical/Redesign PCB 3.0/PCB design/Test 09. With ESP module/order/capture_001.png

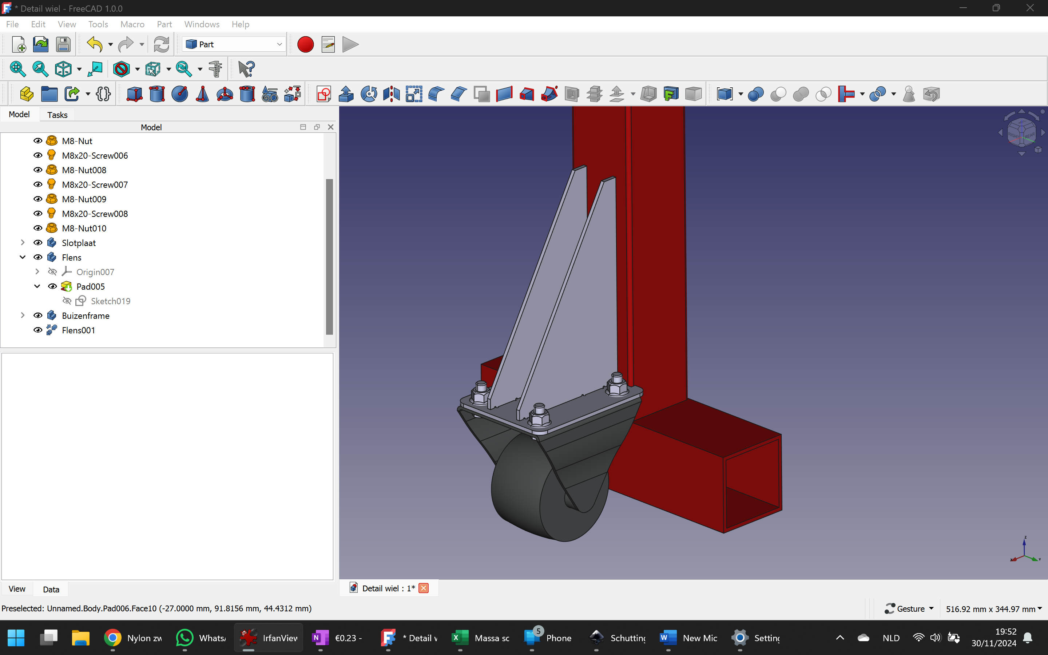
04 Electrical/Redesign PCB 3.0/PCB design/Test 09. With ESP module/order/capture_001.png
