henkjannl/RoomThermostat/04 Electrical/Redesign PCB 3.0/PCB design/V3.0 Ordered at JLCPCB/order/New.png

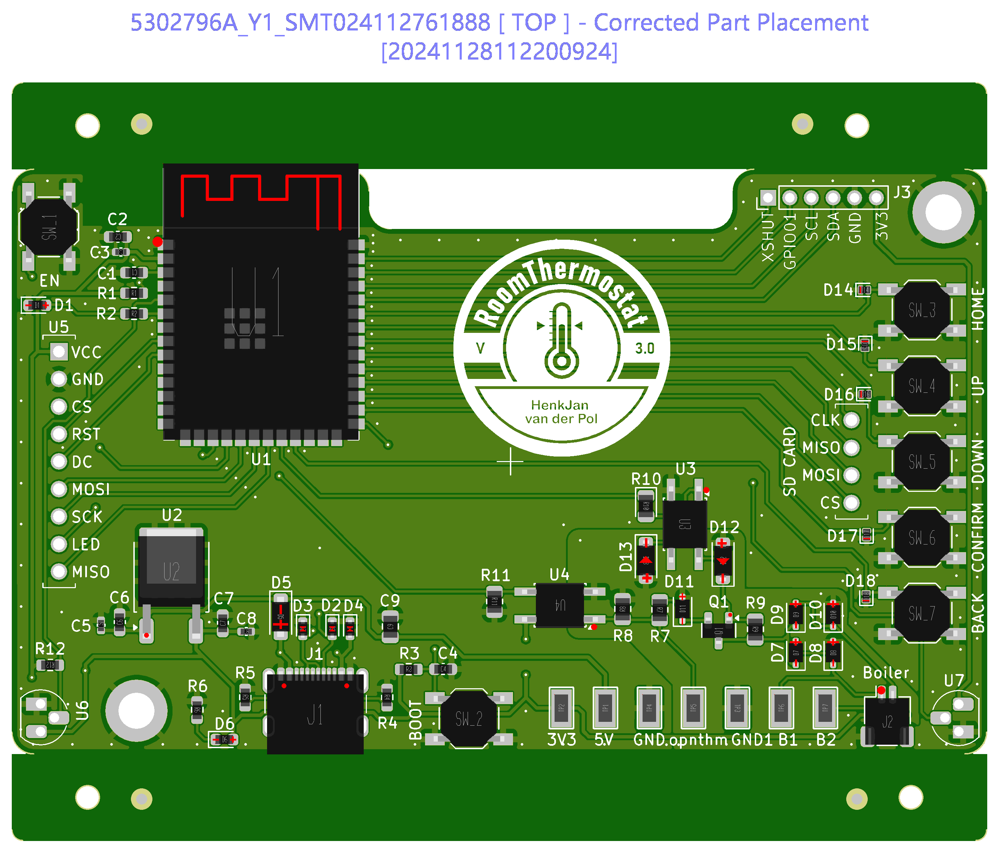
04 Electrical/Redesign PCB 3.0/PCB design/V3.0 Ordered at JLCPCB/order/New.png
