henkjannl/RoomThermostat/04 Electrical/Redesign PCB 3.0/PCB design/V3.1 Not yet ordered/order/capture_005.png

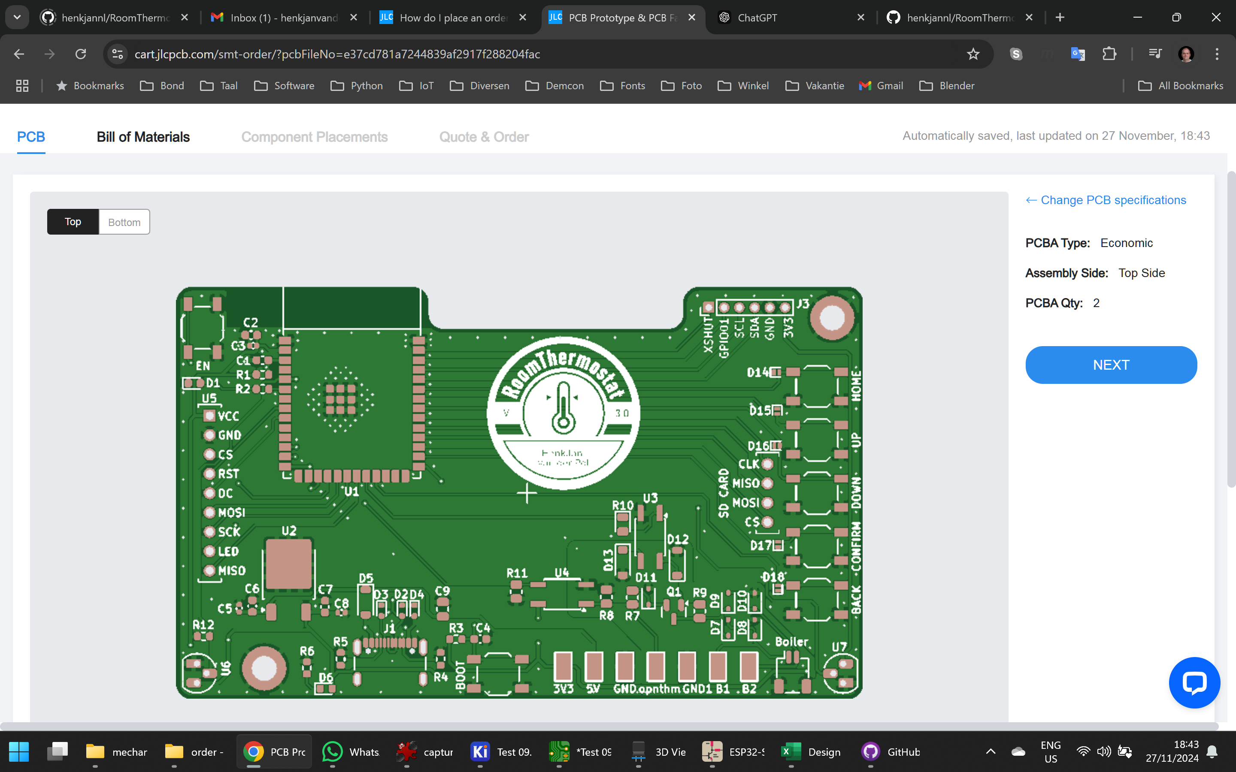
04 Electrical/Redesign PCB 3.0/PCB design/V3.1 Not yet ordered/order/capture_005.png
