henkjannl/RoomThermostat/03 Mechanical/Components/Dallas DS18B20.step

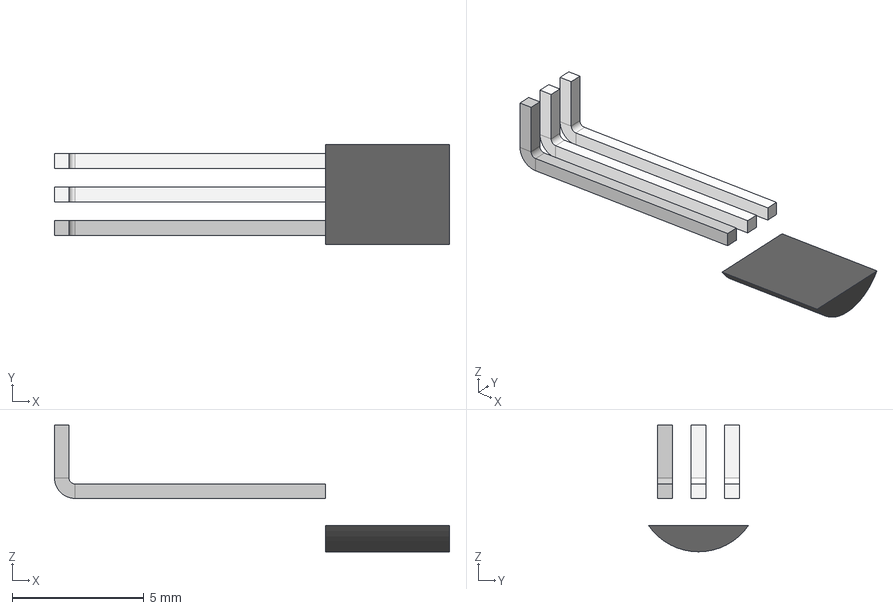
[picture p150: CAD file, 2022-12-05]
03 Mechanical/Components/Dallas DS18B20.step
15.0 x 3.79 x 4.80 mm
DallasSensor
DallasPin002
DallasPin003
DallasPin001
