henkjannl/RoomThermostat/03 Mechanical/Housing for TTGO and Opentherm/DallasSensor.FCStd

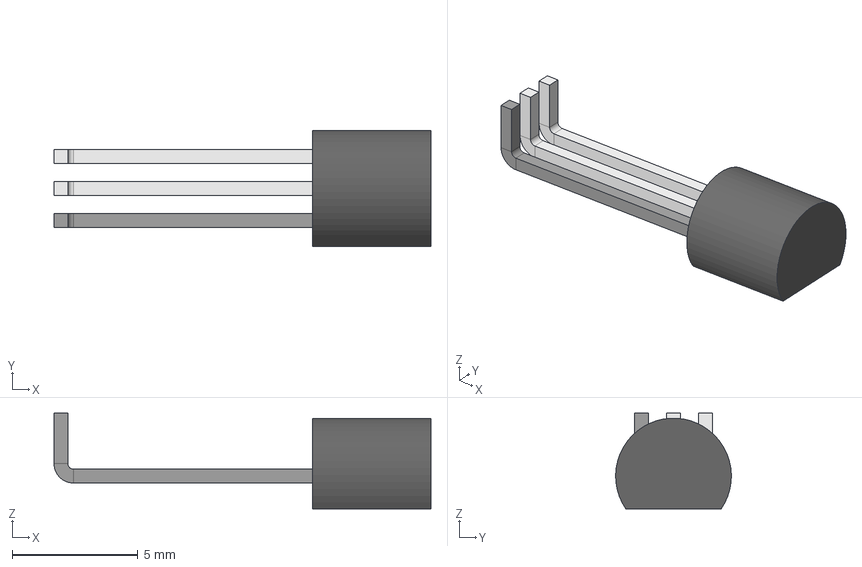
[picture p151: CAD file, 2022-12-05]
03 Mechanical/Housing for TTGO and Opentherm/DallasSensor.FCStd
15.0 x 4.60 x 3.80 mm
DallasSensor
DallasPin002
DallasPin003
DallasPin001
