henkjannl/RoomThermostat/03 Mechanical/Screw interface.3mf

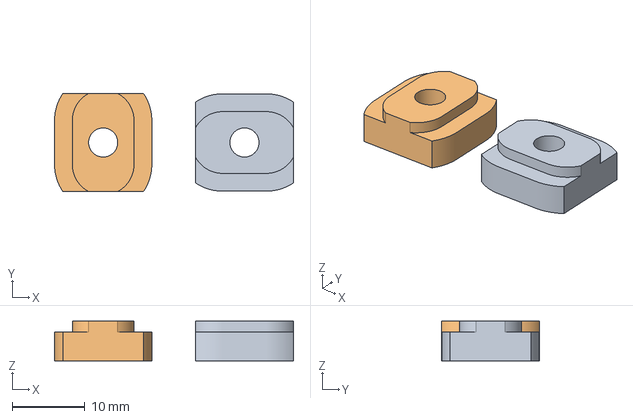
[picture p152: CAD file, 2023-01-13]
03 Mechanical/Screw interface.3mf
32.9 x 13.5 x 5.50 mm
Screw interface.stl
ScrewInterface.stl
