henkjannl/RoomThermostat/03 Mechanical/Housing for TTGO and Opentherm/SelftappingScrew3.0x10.FCStd

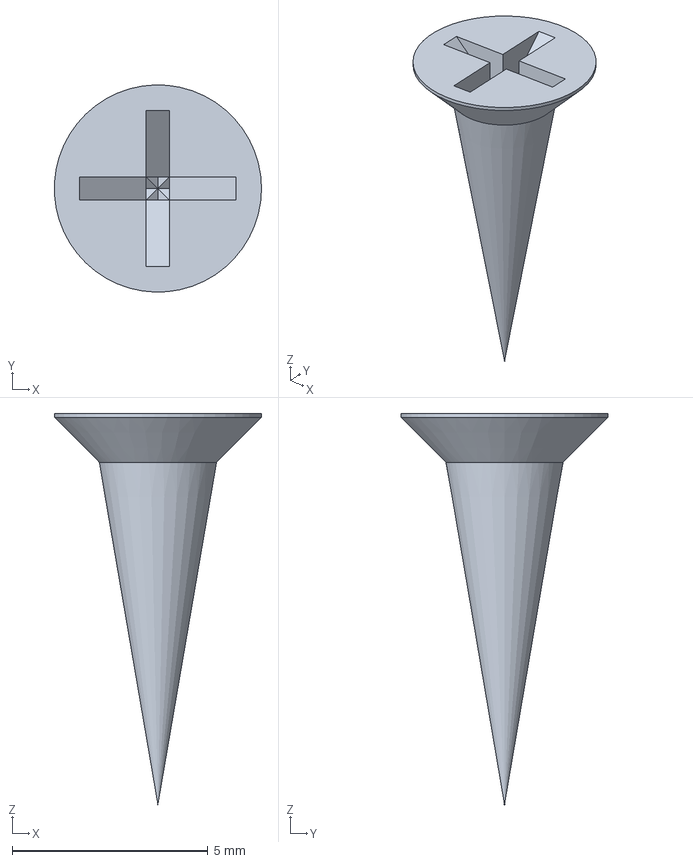
[picture p153: CAD file, 2022-12-05]
03 Mechanical/Housing for TTGO and Opentherm/SelftappingScrew3.0x10.FCStd
5.29 x 5.30 x 10.0 mm
