henkjannl/RoomThermostat/07 Readonly/DIYless opentherm shield/Wiring.png

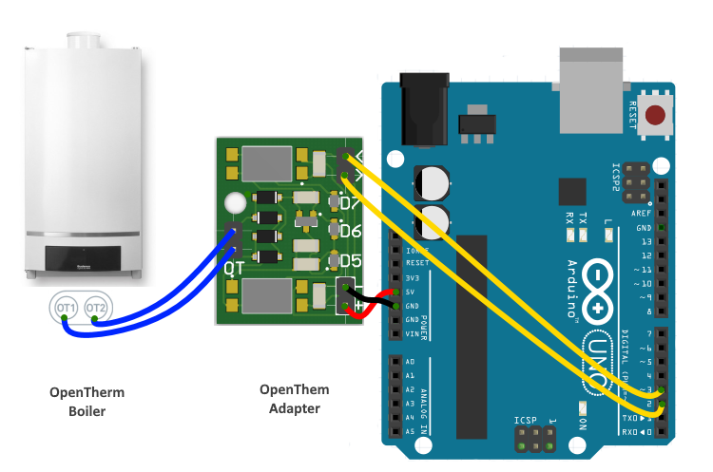
07 Readonly/DIYless opentherm shield/Wiring.png
