henkjannl/RoomThermostat/05 Software/Tests/Test10_testKeyboard/Measurements.xlsx

Sheet: Sheet1
1000000 | Hz
30 | Hz
33333.33333
24.23
8.77
16.5
15.46

Sheet: Sheet2
UP | SELECT | DOWN
74 | 75 | 87 | SELECT
74 | 17 | 87
74 | 25 | 87
74 | 94 | 85
74 | 95 | 86 | UP
33 | 95 | 86
30 | 95 | 86
24 | 95 | 86
74 | 95 | 86
74 | 94 | 45 | DOWN
74 | 94 | 33
74 | 94 | 28
74 | 95 | 85
74 | 80 | 87 | SELECT
74 | 4 | 87
74 | 7 | 87
74 | 7 | 87
74 | 94 | 85
74 | 94 | 85 | DOWN
74 | 94 | 38
74 | 95 | 35
74 | 94 | 35
74 | 94 | 30
74 | 94 | 28
74 | 94 | 27
74 | 94 | 33
74 | 95 | 0
74 | 95 | 86
74 | 95 | 86
74 | 95 | 85
74 | 95 | 86
74 | 95 | 86
74 | 95 | 86
74 | 94 | 85
10 | 96 | 84
73 | 88 | 82 | SELECT
74 | 9 | 85
74 | 97 | 86
69 | 95 | 85 | UP
16 | 94 | 84
74 | 95 | 84 | DOWN
73 | 94 | 30
74 | 95 | 85 | SELECT
74 | 19 | 73
74 | 94 | 84 | DOWN
74 | 95 | 51 | UP
37 | 95 | 85
74 | 95 | 85
74 | 95 | 85
74 | 95 | 85
74 | 95 | 85
