henkjannl/RoomThermostat/04 Electrical/Redesign PCB 3.0/PCB design/Test 06. Simplified interface/Results/r1-4.csv

time | P(R1) | P(R2) | P(R3) | P(R4)
0 | 0.00974283 | 0.00730074 | 0.00130759 | 1.88245e-19
1e-08 | 0.00974895 | 0.00730077 | 0.00130764 | 1.88544e-19
2e-08 | 0.00975635 | 0.00730084 | 0.00130769 | 1.88544e-19
4e-08 | 0.00977161 | 0.00730105 | 0.00130778 | 1.88544e-19
8e-08 | 0.00980242 | 0.00730191 | 0.00130797 | 1.88544e-19
1.6e-07 | 0.00986396 | 0.00730536 | 0.00130835 | 1.88544e-19
3.2e-07 | 0.00998765 | 0.0073187 | 0.00130911 | 1.88544e-19
6.4e-07 | 0.0102367 | 0.00736813 | 0.00131063 | 1.88544e-19
1.28e-06 | 0.0107482 | 0.0075393 | 0.00131362 | 1.88544e-19
2.28e-06 | 0.0115701 | 0.00794079 | 0.00131819 | 1.88544e-19
3.28e-06 | 0.0124228 | 0.00844682 | 0.00132265 | 1.88544e-19
4.28e-06 | 0.013306 | 0.00901067 | 0.001327 | 1.88544e-19
5.28e-06 | 0.01422 | 0.00960091 | 0.00133123 | 1.88544e-19
6.28e-06 | 0.0151646 | 0.0101882 | 0.00133537 | 1.88544e-19
7.28e-06 | 0.01614 | 0.0107407 | 0.0013394 | 1.88544e-19
8.28e-06 | 0.0171459 | 0.0112296 | 0.00134333 | 1.88544e-19
9.28e-06 | 0.0181827 | 0.0116426 | 0.00134717 | 1.88544e-19
1.028e-05 | 0.0192499 | 0.0119879 | 0.00135091 | 1.88544e-19
1.128e-05 | 0.0203479 | 0.0122833 | 0.00135458 | 1.88544e-19
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
