henkjannl/RoomThermostat/04 Electrical/Redesign PCB 3.0/PCB design/V3.1 Not yet ordered/Results/D7.csv

time | I(D7) | P(D7)
0 | -1.12025e-11 | 4.27474e-11
2e-08 | -1.12472e-11 | 4.2918e-11
4e-08 | -1.12472e-11 | 4.2918e-11
8e-08 | -1.12472e-11 | 4.2918e-11
1.6e-07 | -1.12472e-11 | 4.2918e-11
3.2e-07 | -1.12472e-11 | 4.2918e-11
6.4e-07 | -1.12472e-11 | 4.2918e-11
1.28e-06 | -1.12472e-11 | 4.2918e-11
2.56e-06 | -1.12472e-11 | 4.2918e-11
4.56e-06 | -1.12472e-11 | 4.2918e-11
6.56e-06 | -1.12472e-11 | 4.2918e-11
8.56e-06 | -1.12472e-11 | 4.2918e-11
1.056e-05 | -1.12472e-11 | 4.2918e-11
1.256e-05 | -1.12472e-11 | 4.2918e-11
1.456e-05 | -1.12472e-11 | 4.2918e-11
1.656e-05 | -1.12472e-11 | 4.2918e-11
1.856e-05 | -1.12472e-11 | 4.2918e-11
2.056e-05 | -1.12472e-11 | 4.2918e-11
2.256e-05 | -1.12472e-11 | 4.2918e-11
2.456e-05 | -1.12472e-11 | 4.2918e-11
2.656e-05 | -1.12472e-11 | 4.2918e-11
2.856e-05 | -1.12472e-11 | 4.2918e-11
3.056e-05 | -1.12472e-11 | 4.2918e-11
3.256e-05 | -1.12472e-11 | 4.2918e-11
3.456e-05 | -1.12472e-11 | 4.2918e-11
3.656e-05 | -1.12472e-11 | 4.2918e-11
3.856e-05 | -1.12472e-11 | 4.2918e-11
4.056e-05 | -1.12472e-11 | 4.2918e-11
4.256e-05 | -1.12472e-11 | 4.2918e-11
4.456e-05 | -1.12472e-11 | 4.2918e-11
4.656e-05 | -1.12472e-11 | 4.2918e-11
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
