henkjannl/RoomThermostat/04 Electrical/Redesign PCB 3.0/PCB design/V3.1 Not yet ordered/Results/Opentherm simulation.csv

time | V(b+) | V(b-)
0 | -0.802399 | 16.3875
1e-08 | -0.802435 | 16.3875
2e-08 | -0.802471 | 16.3875
4e-08 | -0.802544 | 16.3876
8e-08 | -0.802688 | 16.3876
1.6e-07 | -0.802978 | 16.3878
3.2e-07 | -0.803556 | 16.3881
6.4e-07 | -0.80471 | 16.3888
1.28e-06 | -0.807011 | 16.3901
2.28e-06 | -0.810587 | 16.3921
3.28e-06 | -0.814142 | 16.394
4.28e-06 | -0.817676 | 16.3959
5.28e-06 | -0.821191 | 16.3977
6.28e-06 | -0.824687 | 16.3995
7.28e-06 | -0.828165 | 16.4012
8.28e-06 | -0.831627 | 16.4029
9.28e-06 | -0.835073 | 16.4046
1.028e-05 | -0.838504 | 16.4062
1.128e-05 | -0.841921 | 16.4078
1.228e-05 | -0.845324 | 16.4093
1.328e-05 | -0.848714 | 16.4108
1.428e-05 | -0.852091 | 16.4123
1.528e-05 | -0.855456 | 16.4137
1.628e-05 | -0.85881 | 16.4151
1.728e-05 | -0.862153 | 16.4165
1.828e-05 | -0.865485 | 16.4179
1.928e-05 | -0.868807 | 16.4192
2.028e-05 | -0.872119 | 16.4206
2.128e-05 | -0.875421 | 16.4219
2.228e-05 | -0.878715 | 16.4231
2.328e-05 | -0.882 | 16.4244
2.428e-05 | -0.885277 | 16.4256
2.528e-05 | -0.888545 | 16.4268
2.628e-05 | -0.891806 | 16.428
2.728e-05 | -0.895059 | 16.4292
2.828e-05 | -0.898304 | 16.4304
2.928e-05 | -0.901543 | 16.4315
3.028e-05 | -0.904774 | 16.4327
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
