henkjannl/RoomThermostat/04 Electrical/Redesign PCB 3.0/PCB design/V3.1 Not yet ordered/Results/QU1.csv

time | I(D7) | P(QU1)
0 | -1.12038e-11 | 2.37704e-10
2e-08 | -1.12868e-11 | 2.37704e-10
4e-08 | -1.12868e-11 | 2.37705e-10
8e-08 | -1.12868e-11 | 2.37704e-10
1.6e-07 | -1.12868e-11 | 2.37705e-10
3.2e-07 | -1.12868e-11 | 2.37705e-10
6.4e-07 | -1.12868e-11 | 2.37706e-10
1.28e-06 | -1.12868e-11 | 2.37707e-10
2.56e-06 | -1.12868e-11 | 2.3771e-10
4.56e-06 | -1.12868e-11 | 2.37715e-10
6.56e-06 | -1.12868e-11 | 2.37719e-10
8.56e-06 | -1.12868e-11 | 2.37723e-10
1.056e-05 | -1.12868e-11 | 2.37727e-10
1.256e-05 | -1.12868e-11 | 2.37731e-10
1.456e-05 | -1.12868e-11 | 2.37734e-10
1.656e-05 | -1.12868e-11 | 2.37738e-10
1.856e-05 | -1.12868e-11 | 2.37741e-10
2.056e-05 | -1.12868e-11 | 2.37745e-10
2.256e-05 | -1.12868e-11 | 2.37748e-10
2.456e-05 | -1.12868e-11 | 2.37751e-10
2.656e-05 | -1.12868e-11 | 2.37755e-10
2.856e-05 | -1.12868e-11 | 2.37758e-10
3.056e-05 | -1.12868e-11 | 2.37761e-10
3.256e-05 | -1.12868e-11 | 2.37764e-10
3.456e-05 | -1.12868e-11 | 2.37767e-10
3.656e-05 | -1.12868e-11 | 2.3777e-10
3.856e-05 | -1.12868e-11 | 2.37773e-10
4.056e-05 | -1.12868e-11 | 2.37775e-10
4.256e-05 | -1.12868e-11 | 2.37778e-10
4.456e-05 | -1.12868e-11 | 2.37781e-10
4.656e-05 | -1.12868e-11 | 2.37784e-10
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
