henkjannl/RoomThermostat/04 Electrical/Redesign PCB 3.0/PCB design/V3.1 Not yet ordered/Results/d1-4 current.csv

time | I(D4) | I(D5) | I(D6) | I(D7)
0 | 0.009 | -2.45239e-12 | -0.00202045 | -1.12026e-11
1e-08 | 0.00900279 | -2.45315e-12 | -0.00202051 | -1.12116e-11
2e-08 | 0.00900559 | -2.45315e-12 | -0.00202058 | -1.12116e-11
4e-08 | 0.00901119 | -2.45493e-12 | -0.00202071 | -1.12116e-11
8e-08 | 0.00902239 | -2.4567e-12 | -0.00202093 | -1.12116e-11
1.6e-07 | 0.0090448 | -2.46025e-12 | -0.00202133 | -1.12116e-11
3.2e-07 | 0.0090896 | -2.46914e-12 | -0.00202212 | -1.12116e-11
6.4e-07 | 0.0091792 | -2.49401e-12 | -0.0020237 | -1.12116e-11
1.28e-06 | 0.0093584 | -2.54019e-12 | -0.00202682 | -1.12116e-11
2.28e-06 | 0.0096384 | -2.6219e-12 | -0.00203162 | -1.12116e-11
3.28e-06 | 0.0099184 | -2.7125e-12 | -0.00203633 | -1.12116e-11
4.28e-06 | 0.0101984 | -2.80487e-12 | -0.00204095 | -1.12116e-11
5.28e-06 | 0.0104784 | -2.89724e-12 | -0.00204549 | -1.12116e-11
6.28e-06 | 0.0107584 | -2.98961e-12 | -0.00204995 | -1.12116e-11
7.28e-06 | 0.0110384 | -3.07665e-12 | -0.00205434 | -1.12116e-11
8.28e-06 | 0.0113184 | -3.16014e-12 | -0.00205865 | -1.12116e-11
9.28e-06 | 0.0115984 | -3.2383e-12 | -0.00206289 | -1.12116e-11
1.028e-05 | 0.0118784 | -3.31291e-12 | -0.00206707 | -1.12116e-11
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
