henkjannl/RoomThermostat/04 Electrical/Redesign PCB 3.0/PCB design/V3.1 Not yet ordered/Results/d1-4 power.csv

time | P(D1) | P(D2) | P(D3) | P(D4)
0 | 0.00641159 | 2.68713e-10 | 2.68713e-10 | 0.00641159
1e-08 | 0.00641365 | 8.71055e-08 | 8.71055e-08 | 0.00641365
2e-08 | 0.00641572 | 8.32736e-08 | 8.32736e-08 | 0.00641572
4e-08 | 0.00641986 | 8.22307e-08 | 8.22307e-08 | 0.00641986
8e-08 | 0.00642813 | 8.22568e-08 | 8.22568e-08 | 0.00642813
1.6e-07 | 0.00644468 | 8.15393e-08 | 8.15393e-08 | 0.00644468
3.2e-07 | 0.00647778 | 8.16529e-08 | 8.16529e-08 | 0.00647778
6.4e-07 | 0.00654399 | 8.04956e-08 | 8.04956e-08 | 0.00654399
1.28e-06 | 0.00667653 | 7.95277e-08 | 7.95277e-08 | 0.00667653
2.28e-06 | 0.00688377 | 7.69149e-08 | 7.69149e-08 | 0.00688377
3.28e-06 | 0.00709124 | 7.52837e-08 | 7.52837e-08 | 0.00709124
4.28e-06 | 0.00729891 | 7.28437e-08 | 7.28437e-08 | 0.00729891
5.28e-06 | 0.00750679 | 7.13927e-08 | 7.13927e-08 | 0.00750679
6.28e-06 | 0.00771487 | 6.91261e-08 | 6.9126e-08 | 0.00771487
7.28e-06 | 0.00792315 | 6.78222e-08 | 6.78223e-08 | 0.00792315
8.28e-06 | 0.00813162 | 6.57045e-08 | 6.57045e-08 | 0.00813162
9.28e-06 | 0.00834028 | 6.45646e-08 | 6.45646e-08 | 0.00834028
1.028e-05 | 0.00854912 | 6.26396e-08 | 6.26396e-08 | 0.00854912
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
