henkjannl/RoomThermostat/04 Electrical/Redesign PCB 3.0/PCB design/V3.1 Not yet ordered/Results/Power D1...D4.png

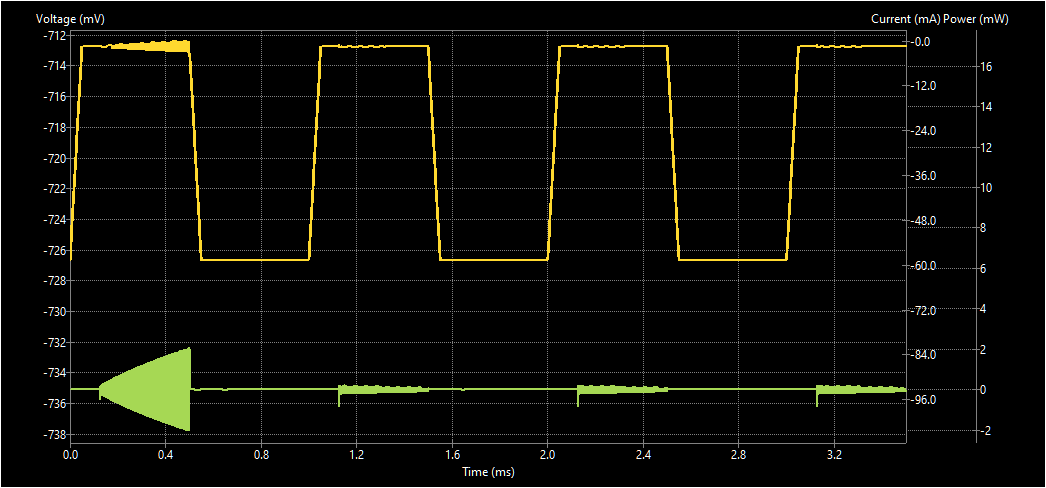
04 Electrical/Redesign PCB 3.0/PCB design/V3.1 Not yet ordered/Results/Power D1...D4.png
