henkjannl/RoomThermostat/05 Software/Tests/Test08_monitor_chromoterm/Request and answer.bmp

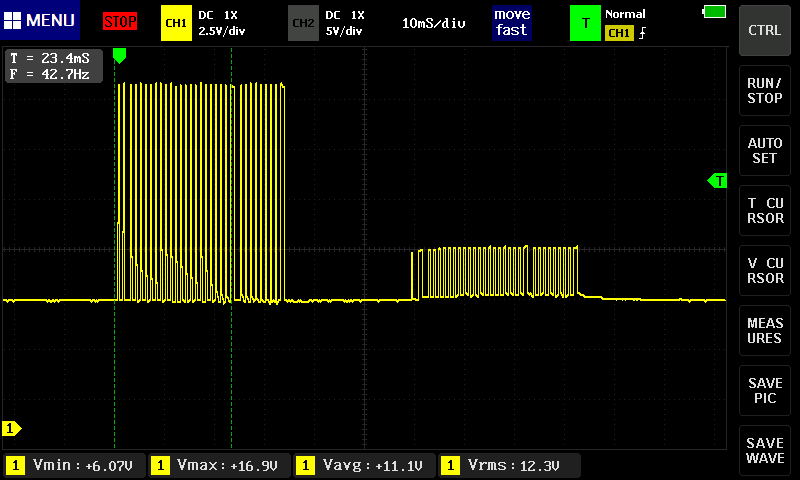
05 Software/Tests/Test08_monitor_chromoterm/Request and answer.bmp
