henkjannl/RoomThermostat/05 Software/Tests/Test08_monitor_chromoterm/Request.bmp

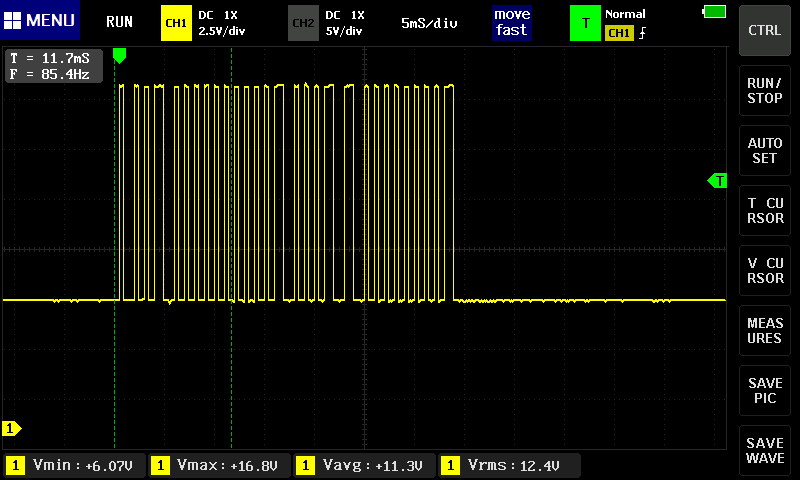
05 Software/Tests/Test08_monitor_chromoterm/Request.bmp
