henkjannl/RoomThermostat/05 Software/Tests/Test19_SendLogfileFromTelegram/data/box.jpg

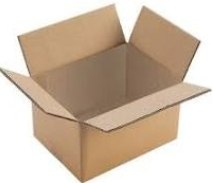
05 Software/Tests/Test19_SendLogfileFromTelegram/data/box.jpg
