henkjannl/RoomThermostat/05 Software/Tests/Test19_SendLogfileFromTelegram/data/shaarda.jpg

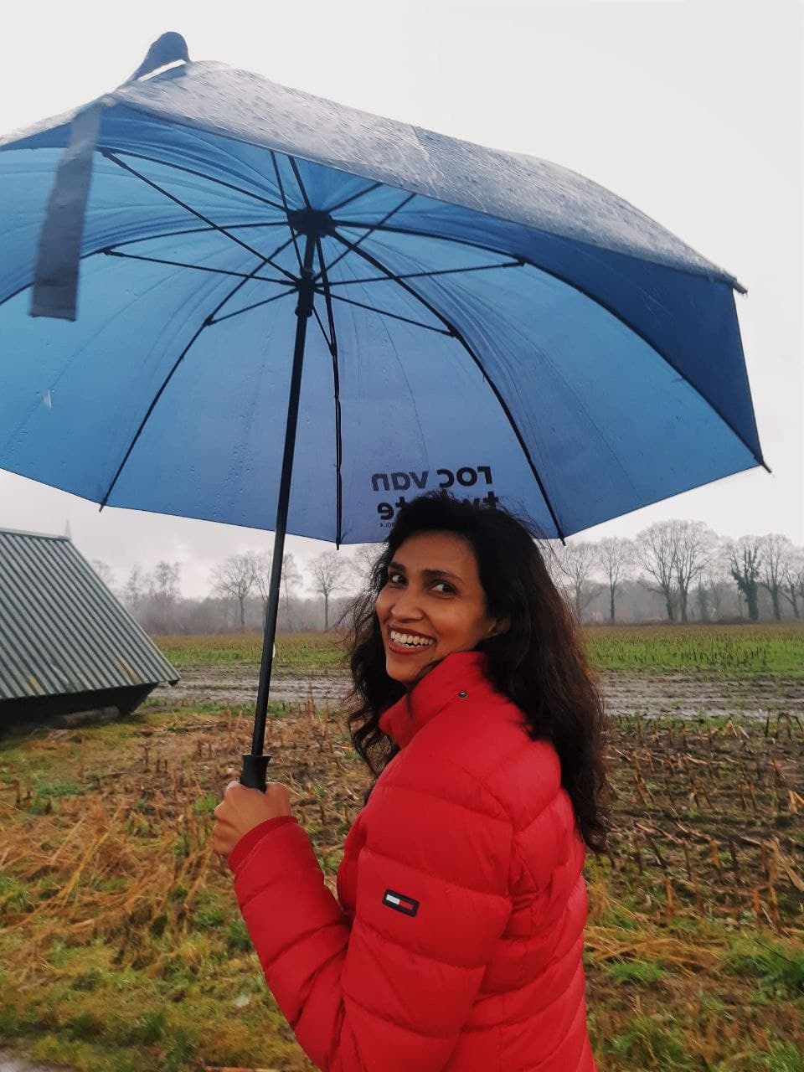
05 Software/Tests/Test19_SendLogfileFromTelegram/data/shaarda.jpg
