henkjannl/RoomThermostat/05 Software/Tests/_UniversalTelegramIssue181/data/box.jpg

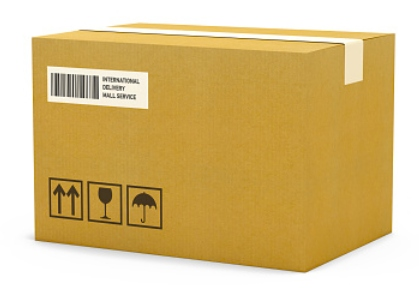
05 Software/Tests/_UniversalTelegramIssue181/data/box.jpg
