henkjannl/RoomThermostat/07 Readonly/Dallas DS18B20/TO92 package dimensions.PDF

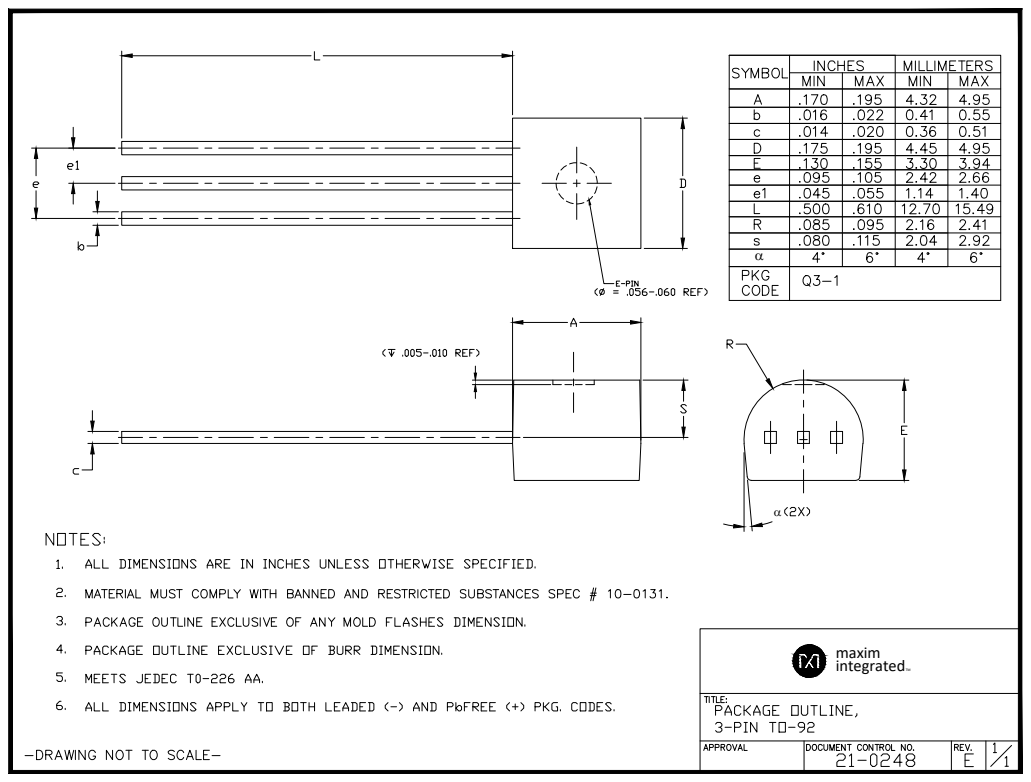
[picture p166: page 1]
maxim integratedTM
