henkjannl/RoomThermostat/07 Readonly/Phoenix connector/Phoenix MSTB 2,5 2-ST cable part/pxc_1754449_06_MSTB-2-5-2-ST_FAM.pdf

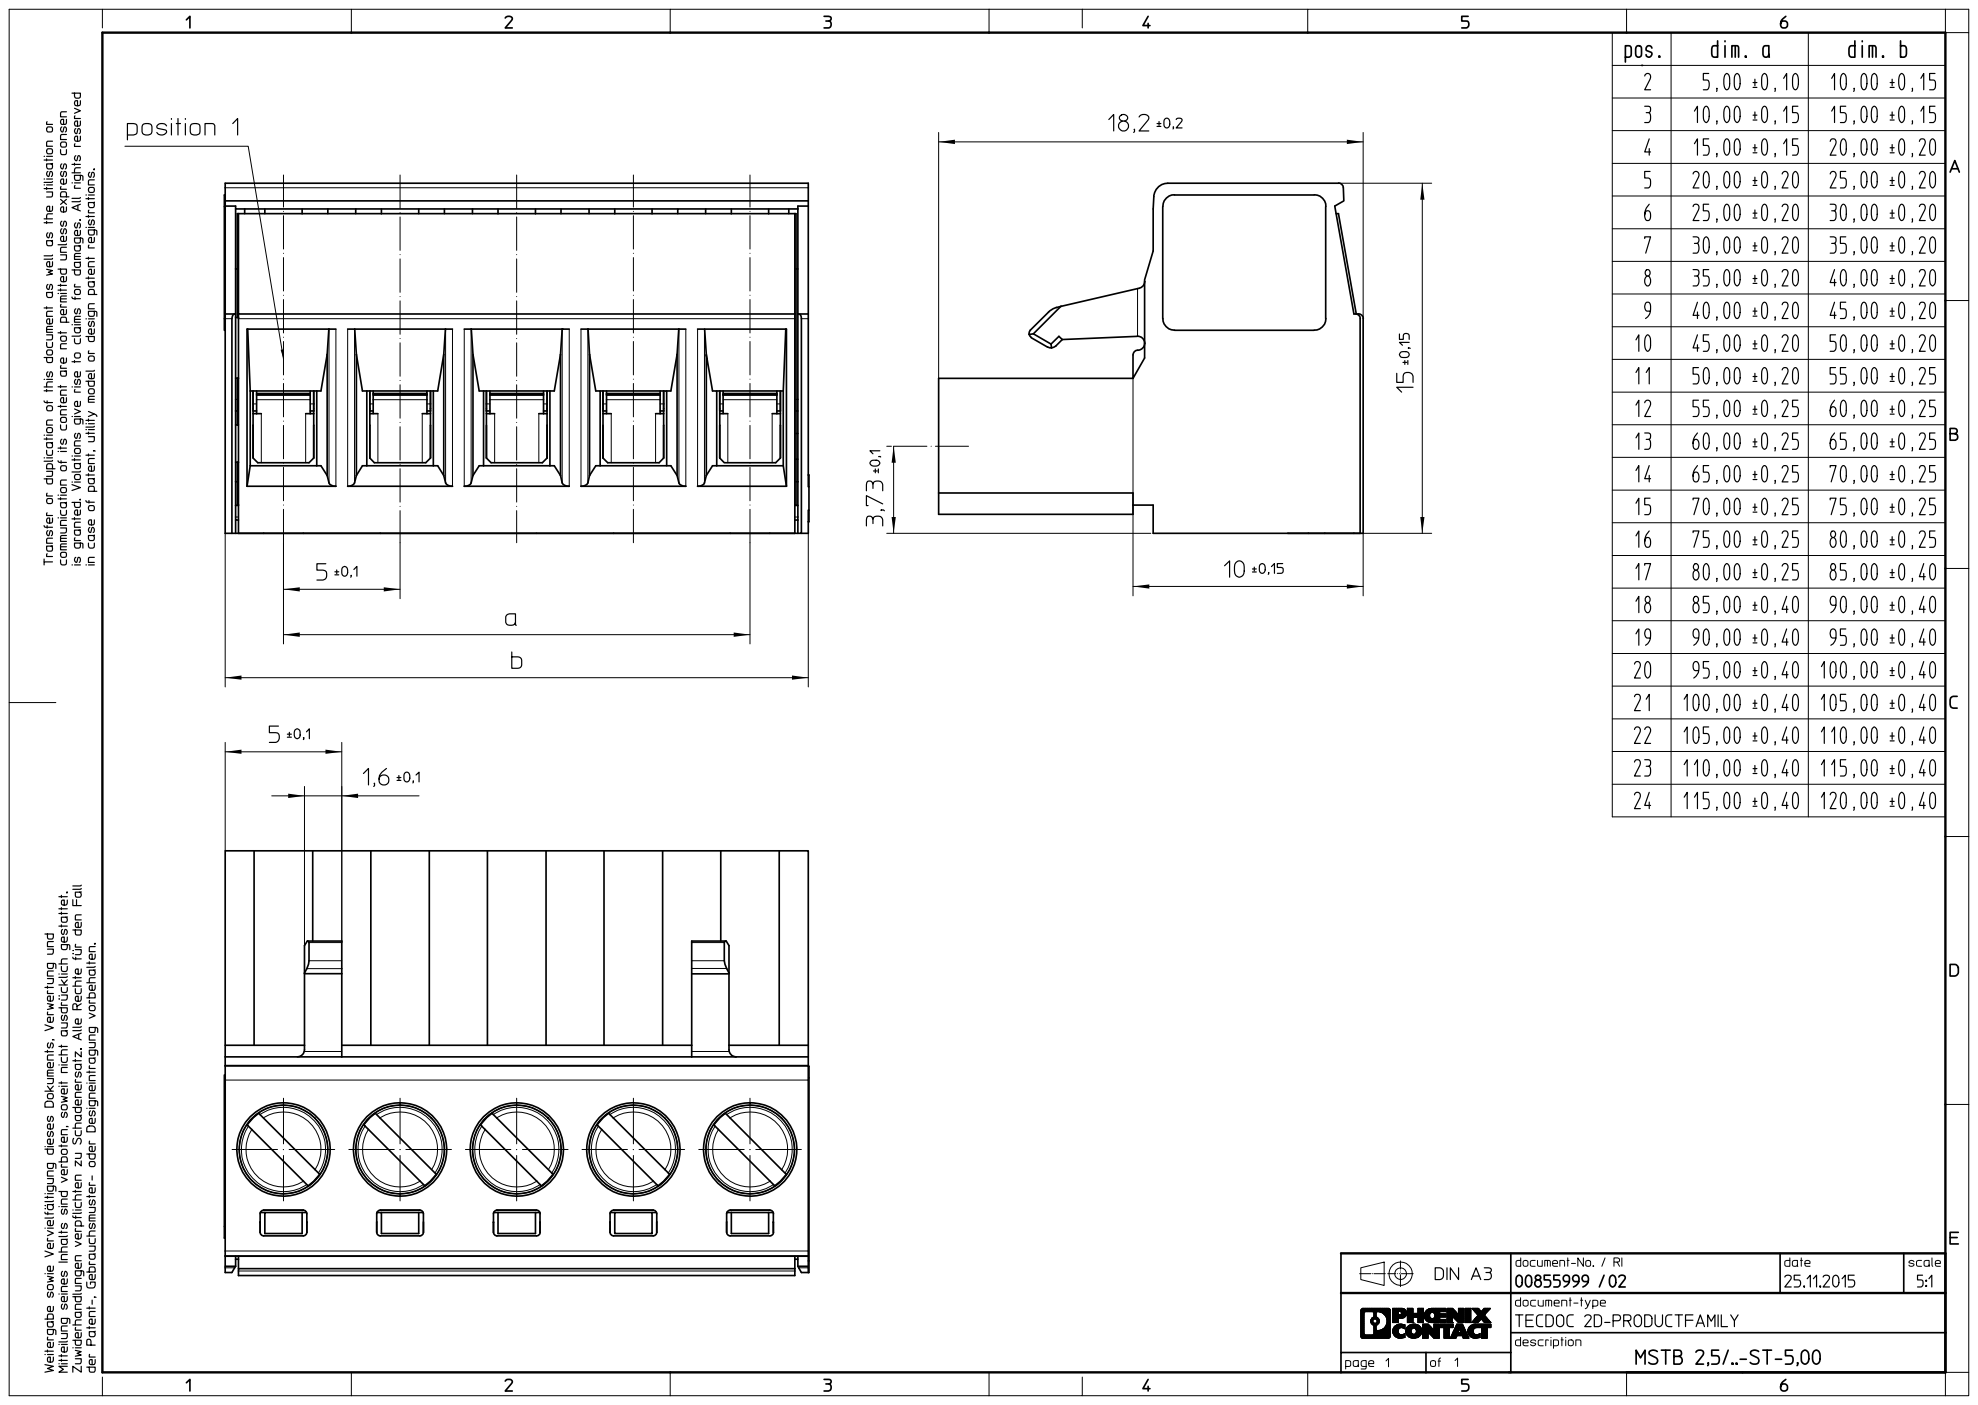
[picture p167: page 1]
