henkjannl/RoomThermostat/07 Readonly/Phoenix connector/Phoenix MSTB-2,5-2-G PCB part/pxc_1754436_04_MSTB-2-5-2-G_FAM.pdf

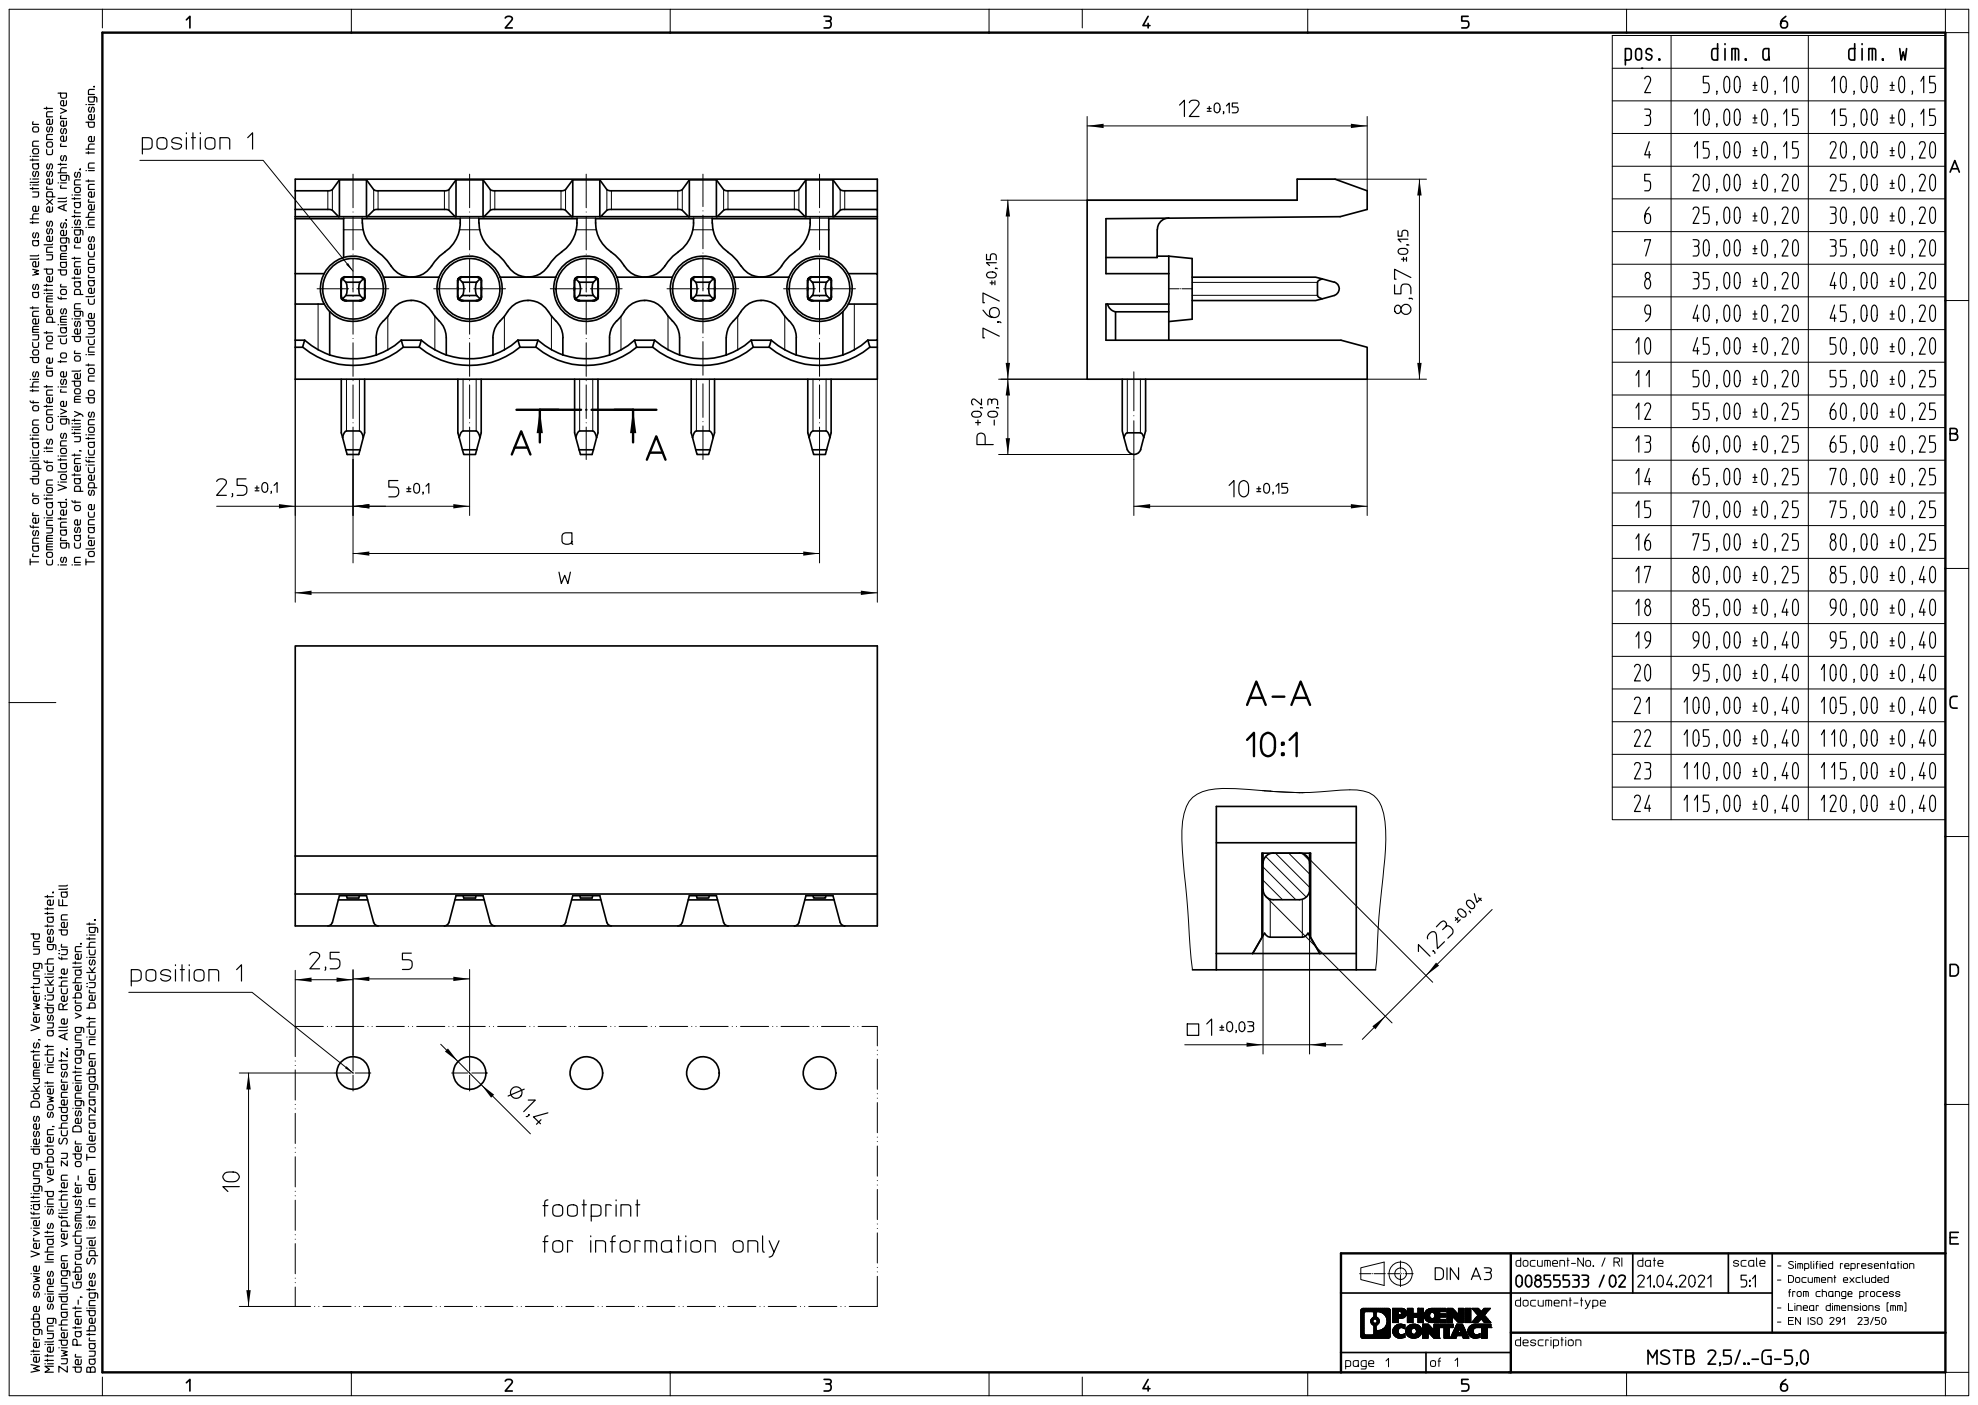
[picture p168: page 1]
