henkjannl/RoomThermostat/05 Software/Roomthermostat V2/Roomthermostat V2.0/src/h_temperature.h

#pragma once

#include <OneWire.h>
#include <DallasTemperature.h>
#include <OpenTherm.h>

#define RECONNECT_INTERVAL   5*60*1000
#define TEMP_MEAS_INTERVAL     10*1000 
#define BOILER_INTERVAL         5*1000 

/* ======================================
   PID CONTROLLER CLASS DEFINITION
   ====================================== */
class PID {
  public:
    float KP = 10;
    float KI = 0.02;  
    float KD = 0;

    // Upper and lower bounds on requested boiler temperature
    float outputHigh = 60;
    float outputLow  =  5;
      
    float setpoint=4.0;
    
    unsigned long currentTime;
    unsigned long previousTime;
    
    float currentTemperature;
    float previousTemperature;

    float boilerTemperature;
    float boilerPercentage;

    float timeStep;

    float ierr = 0;
    float previousError = 0;
    float derivative = 0;

    float P;
    float I;
    float D;
    
    float newValue(float newTemperature);
};

float PID::newValue(float newTemperature) {

  // Update temperature
  previousTemperature = currentTemperature;
  currentTemperature  = newTemperature;

  // Store time in native format to ensure right outcome on millis() overflow 
  previousTime=currentTime;
  currentTime=millis();
  timeStep=(currentTime-previousTime)/1000; // converted to seconds here
    
  // Calculate the control error
  float error = setpoint - currentTemperature;
  
  // Calculate the integral error
  ierr += error * timeStep;  
  
  // !! D-action probably not implemented well yet !!
  // perhaps we need to filter the signal to prevent noise in the D-action
  // Calculate the measurement derivative
  derivative = (timeStep!=0) ? (error - previousError) / timeStep : 0;
  
  // Calculate the PID output
  P = KP * error;        // proportional contribution
  I = KI * ierr;         // integral contribution  
  D = KD * derivative;   // differential contribution
  boilerTemperature = P+I+D;
  
  // Implement anti-windup
  // !! Should the (error<0) clause be there? !! What does it do?
  if ((boilerTemperature < outputLow)  and (error<0)) ierr -= error * timeStep;    
  if ((boilerTemperature > outputHigh) and (error>0)) ierr -= error * timeStep;    
  
  // Clip output
  boilerTemperature = max(outputLow, min(outputHigh, boilerTemperature));
  boilerPercentage=(boilerTemperature-outputLow)/(outputHigh-outputLow);
  
  //Serial.printf("setpoint= %.3f°C measured=%.3f°C P=%.3f I=%.3f D=%.3f boiler=%.3f°C\n",setpoint, currentTemperature, P, I, D, boilerTemperature);

  previousError = error;

  return boilerTemperature;
};

/* ======================================
   GLOBAL VARIABLES
   ====================================== */
OneWire oneWire(PIN_ONE_WIRE_BUS);                         // Bus for the temperature sensors 
DallasTemperature dallasSensor(&oneWire);                  // Driver for temperature sensors
OpenTherm opentherm(PIN_OPENTHERM_IN, PIN_OPENTHERM_OUT);  // Driver for boiler
PID pidController;    

//Interrupthandler for OpenTherm
void ICACHE_RAM_ATTR handleInterrupt() {
  opentherm.handleInterrupt();
}


void TemperatureMeasure() {
  float measuredTemperature;
  float sum = 0;
  int   cnt = 0;
  
  controllerData.temperatureMeasurementOK = true;

  //controllerData.logBusyTime.start(btTemperature);

  dallasSensor.requestTemperatures();

  for (int i=0; i<controllerData.numSensors; i++) {
    measuredTemperature=dallasSensor.getTempC(controllerData.sensorAddress[i]);
    if(measuredTemperature!=DEVICE_DISCONNECTED_C) {
      sum+=measuredTemperature;
      cnt++;
    }
    else Serial.printf("Sensor %d not connected ", i);
  };

  // We're happy if at least one sensor is left
  if( cnt<1 ) controllerData.temperatureMeasurementOK = false;

  if(controllerData.temperatureMeasurementOK) {
    measuredTemperature = sum/cnt;    
    if(measuredTemperature < -40) controllerData.temperatureMeasurementOK = false;
  }

  // Only update raw temperture if all went well
  if ( controllerData.temperatureMeasurementOK ) {
    controllerData.rawTemperature = measuredTemperature;
    controllerData.lastTemperatureMeasurement = timeNow();
  }

  //controllerData.logBusyTime.finish(btTemperature);  
}


void TemperatureSensorConnect() {
  
  // Initialize thermometer
  dallasSensor.begin();

  controllerData.numSensors=dallasSensor.getDeviceCount();
  Serial.printf("%d device(s) found on OneWire bus\n", controllerData.numSensors);

  for(int i=0; i<controllerData.numSensors; i++) {

    if ( (i<MAX_NUM_SENSORS) and dallasSensor.getAddress(controllerData.sensorAddress[i], i) ) {
      
        Serial.print("Dallas 18B20 found on address:\t");
        for (uint8_t j = 0; j < 8; j++) Serial.printf("%02X ", controllerData.sensorAddress[i][j]);
        Serial.println();
  
        // Set the therometer precision
        dallasSensor.setResolution(controllerData.sensorAddress[i], TEMPERATURE_PRECISION);
        Serial.printf("Resolution of sensor set to: %d\n",dallasSensor.getResolution(controllerData.sensorAddress[i]));
      }  
  }
    
  Serial.printf("Parasite power on OneWire bus is: %s\n", dallasSensor.isParasitePowerMode() ? "ON": "OFF");
  controllerData.temperatureMeasurementOK = (controllerData.numSensors>0);

  // Do the first temperature measurement
  TemperatureMeasure();
};

void BoilerCommunicate() {  
  static bool  firstEnable                   = true;
  static bool  firstTemperature              = true;
  static bool  lastEnableCentralHeating      = false; 
  static bool  lastEnableHotWater            = false;
  static bool  lastEnableCooling             = false;
  static float lastBoilerTemperatureSetpoint =  -300;
  static float lastDomesticHotWaterSetpoint  =  -300;

  userEventMessage_t message;
  
  unsigned long response;
  
  pidController.setpoint=controllerData.temperatureSetpoint;

  // Ask PID controller for new value
  controllerData.requestedBoilerTemperature = pidController.newValue( controllerData.measuredTemperature() );
  controllerData.boilerPercentage=pidController.boilerPercentage;
  
  controllerData.P          = pidController.P;
  controllerData.I          = pidController.I;
  controllerData.D          = pidController.D;
  controllerData.ierr       = pidController.ierr;
  controllerData.derivative = pidController.derivative;

  // Switch off central heating if it becomes too hot in the room
  controllerData.enableCentralHeating = (controllerData.measuredTemperature() < (controllerData.temperatureSetpoint+2.0));

  // Also switch off heater if we request almost no heat
  if(controllerData.boilerPercentage < 0.05) controllerData.enableCentralHeating=false;

  // Current day and time
  time_t now;
  time(&now); // Get current time
  struct tm * localTime;
  localTime = localtime(&now);
  int currDay = localTime->tm_yday;
  timeValue_t currTime = timeValue_t(localTime->tm_hour, localTime->tm_min);
  
  // Switch keyboard off (just to make sure, potentially not required)
  disableKeyboard(); 

  // Enable central heating
  /*
  if(   firstEnable or 
      ( lastEnableCentralHeating != controllerData.enableCentralHeating ) or 
      ( lastEnableHotWater       != controllerData.enableHotWater       ) or 
      ( lastEnableCooling        != controllerData.enableCooling        ) ) {
        
  */
  if(true) {

    //Serial.printf("BoilerCommunicate()\nEnable boiler\n");
    //response = opentherm.setBoilerStatus(controllerData.enableCentralHeating, controllerData.enableHotWater, controllerData.enableCooling);
    response = opentherm.setBoilerStatus(true, true, false);
    
    switch (opentherm.getLastResponseStatus() ) {

      case OpenThermResponseStatus::SUCCESS:
        Serial.println("Boiler enable response: success");
        firstEnable                         = false;
        controllerData.boilerOnline         = true;
        lastEnableCentralHeating            = controllerData.enableCentralHeating;
        lastEnableHotWater                  = controllerData.enableHotWater;
        lastEnableCooling                   = controllerData.enableCooling;
  
        controllerData.centralHeatingActive = opentherm.isCentralHeatingActive(response);
        controllerData.hotWaterActive       = opentherm.isHotWaterActive(response);
        controllerData.flameOn              = opentherm.isFlameOn(response);
      break;

      case OpenThermResponseStatus::NONE:
        Serial.println("Boiler enable response: none");
        controllerData.boilerOnline         = false;
      break;

      case OpenThermResponseStatus::INVALID:
        Serial.println("Boiler enable response: invalid");
        controllerData.boilerOnline         = false;
      break;

      case OpenThermResponseStatus::TIMEOUT:
        Serial.println("Boiler response: timeout");
        controllerData.boilerOnline         = false;
      break;
    } // switch (opentherm.getLastResponseStatus() )
  } // if firstStatus    
  
  // Set boiler temperature once boiler enable status was successful
  /*
  if( !firstEnable and ( firstTemperature or (controllerData.requestedBoilerTemperature != lastBoilerTemperatureSetpoint) ) ) {
  */

  if(true) {

    Serial.printf("requestedBoilerTemperature %.1f°C\n", controllerData.requestedBoilerTemperature);
    opentherm.setBoilerTemperature(controllerData.requestedBoilerTemperature);

    switch( opentherm.getLastResponseStatus() ) {

      case OpenThermResponseStatus::SUCCESS:
        firstTemperature                = false;
        lastBoilerTemperatureSetpoint   = controllerData.requestedBoilerTemperature; // Update last requested setpoint
        controllerData.boilerResponse   = boilerSuccess;
      break;

      case OpenThermResponseStatus::NONE:
        Serial.println("Boiler response: none");
        controllerData.boilerResponse = boilerNone;
        controllerData.boilerOnline   = false;
      break;

      case OpenThermResponseStatus::INVALID:
        Serial.println("Boiler response: invalid");
        controllerData.boilerResponse = boilerInvalid;
        controllerData.boilerOnline   = false;
      break;

      case OpenThermResponseStatus::TIMEOUT:
        Serial.println("Boiler response: timeout");
        controllerData.boilerResponse = boilerTimeout;
        controllerData.boilerOnline   = false;
      break;
    }
  }

  // Set domestic hot water setpoint
  /*
  if( lastDomesticHotWaterSetpoint != controllerData.requestedDomesticHotWaterSetpoint ) {
  */

  if(true) {

    Serial.printf("requestedDomesticHotWaterSetpoint %.1f°C\n", controllerData.requestedDomesticHotWaterSetpoint);
    opentherm.setDHWSetpoint(controllerData.requestedDomesticHotWaterSetpoint);  
    if (opentherm.getLastResponseStatus() == OpenThermResponseStatus::SUCCESS) {
      Serial.println("Communication success");
      lastDomesticHotWaterSetpoint = controllerData.requestedDomesticHotWaterSetpoint;
    }
  }

  if ( controllerData.boilerOnline ) {
    controllerData.lastBoilerUpdate                  = currTime;
    controllerData.actualBoilerTemperature           = opentherm.getBoilerTemperature();
    Serial.printf("boiler water temperature %.1f°C\n", controllerData.actualBoilerTemperature);
    controllerData.actualDomesticHotWaterTemperature = opentherm.getDHWTemperature();
    //controllerData.boilerPressure                    = opentherm.getPressure();
    controllerData.boilerPressure                    = 0;
  }

  if( controllerData.boilerOnline ) {
    if      (controllerData.boilerPercentage < 0.05) controllerData.dspFlameIcon = iconFlame0; 
    else if (controllerData.boilerPercentage < 0.10) controllerData.dspFlameIcon = iconFlame1; 
    else if (controllerData.boilerPercentage < 0.15) controllerData.dspFlameIcon = iconFlame2; 
    else if (controllerData.boilerPercentage < 0.20) controllerData.dspFlameIcon = iconFlame3; 
    else if (controllerData.boilerPercentage < 0.35) controllerData.dspFlameIcon = iconFlame4; 
    else if (controllerData.boilerPercentage < 0.50) controllerData.dspFlameIcon = iconFlame5; 
    else if (controllerData.boilerPercentage < 0.65) controllerData.dspFlameIcon = iconFlame6; 
    else if (controllerData.boilerPercentage < 0.80) controllerData.dspFlameIcon = iconFlame7; 
    else                                             controllerData.dspFlameIcon = iconFlame8; 
  }
    else controllerData.dspFlameIcon = iconFlame0;


  // Switch keyboard on
  enableKeyboard(); 

  //controllerData.logBusyTime.finish(btOpentherm);  

  controllerData.dspShowerIcon = controllerData.hotWaterActive ? iconShowerOn : iconShowerOff;
  controllerData.dspBoilerIcon = ( controllerData.boilerOnline ) ? iconBoilerConnected : iconBoilerLost;

  if(!controllerData.boilerOnline) {
    controllerData.centralHeatingActive = false;
    controllerData.hotWaterActive       = false;
    controllerData.flameOn              = false;      
    controllerData.dspShowerIcon        = iconShowerOff;
  }

}

void startTemperature() {
  // Connect temperature sensors
  TemperatureSensorConnect();    

  // Start connection with boiler
  opentherm.begin(handleInterrupt);
}

void checkTemperatureIfNeeded() {
  static unsigned long lastTempMeas=0;      // last time temperature measurement was done
  static unsigned long lastReconnect=0;     // last time temperaturesensors were reconnected was done
  static unsigned long lastBoilerConnect=0; // last time boiler was talked to
  userEventMessage_t message;

  // To improve responsiveness, only communicate with the boiler if the backlight is off
  if( !controllerData.backLightOn ) {
    
    if (millis() - lastTempMeas > TEMP_MEAS_INTERVAL) {
      TemperatureMeasure();
  
      // Request controller to calculate new setpoint
      // Send new temperature to display without switching on backlight
      sendMessage(sndTemperature, cmdSilentUpdate, controllerQueue);
      
      lastTempMeas=millis();
    }
  
    if( millis() - lastBoilerConnect > BOILER_INTERVAL ) {
  
      // Request controller to calculate new setpoint
      sendMessage(sndTemperature, cmdBoilerSending, controllerQueue);
      lastBoilerConnect=millis();
    }
  
    if (millis() - lastReconnect > RECONNECT_INTERVAL) {
      if( !controllerData.temperatureMeasurementOK ) TemperatureSensorConnect();
      lastReconnect=millis();
    }
  
    if( xQueueReceive( temperatureQueue, &message, 0) == pdPASS ) {
      Serial.printf("%s > Temperature [%s] k=%d\n", senderLabels[message.sender].c_str(), commandLabels[message.command].c_str(), keyboardEnabed );
      BoilerCommunicate();
      sendMessage(sndTemperature, cmdSilentUpdate, controllerQueue);
    }
  }
}
