henkjannl/RoomThermostat/05 Software/Roomthermostat V2/Roomthermostat V2.0/src/k_display.h

#pragma once
#include <TFT_eSPI.h>
#include <SPI.h>
#include <JPEGDecoder.h>
#include <math.h>

/*********************************************************
 *  Display class                                        *
 *********************************************************/
class Display {
  public:
    Display(TFT_eSPI & tft, ControllerData_t & controllerData, screen_t (*selectedScreen)(), command_t (*selectedMenuItem)() );
    void start();
    void processMessage(const userEventMessage_t message);
    void displayHomeScreen();
    void displayMenuScreen();

  protected:
    TFT_eSPI *tft;
    ControllerData_t *controllerData;
    screen_t (*selectedScreen)();
    command_t (*selectedMenuItem)();
};

Display::Display(TFT_eSPI & tft, ControllerData_t & controllerData, screen_t (*selectedScreen)(), command_t (*selectedMenuItem)() ) {
  // Connect pointers but do not initialize yet
  this->tft              = & tft;
  this->controllerData   = & controllerData;
  this->selectedScreen   = selectedScreen;    // This is a pointer to the menu structure to obtain the current screen
  this->selectedMenuItem = selectedMenuItem;  // This is a pointer to the menu structure to obtain the current menu item
};

void Display::start() {
  // Initialize screen
  disableKeyboard();
  tft->init();
  tft->setRotation(3);
  tft->fillScreen(CLR_BACKGROUND);
  tft->setTextDatum(MC_DATUM);
  // tft->loadFont(FONT_TEMP_MEASURED);
  tft->loadFont(FONT_TEMP_MEASURED, LittleFS);

  tft->setTextColor(CLR_LIGHT_TEXT, CLR_BACKGROUND);
  tft->drawString("Welcome", 160, 120);
  enableKeyboard();
}

void Display::processMessage(const userEventMessage_t message) {
  static screen_t previousScreen = scnSettingsSensorOffset;

  Serial.printf("Display::processMessage() screen: %s menu item: %s\n", screenTitle[selectedScreen()].c_str(), commandLabels[selectedMenuItem()].c_str() );
  //Serial.printf(" previousScreen: %s message.command: %s\n", screenTitle[previousScreen].c_str(), commandLabels[message.command].c_str() );

  if( message.command == cmdBoilerSending) {
      //Serial.println("Display: Icon boiler transmitting");
      if( selectedScreen()==scnHome ) drawJpeg(tft, ICONS[iconBoilerTransmit].c_str(), 6, 78);
  }
  else {

      // Redraw background if screen was changed
      if( selectedScreen() != previousScreen ) {
        if( selectedScreen()==scnHome ) {
          Serial.println("  Redraw homescreen background");
          drawJpeg(tft, "/HomeScreen.jpg", 0,  0);
        }
        else {
          Serial.println("  Fill screen for display of menu");
          tft->fillScreen(CLR_BACKGROUND);
        };
        previousScreen=selectedScreen();
      };

      // Redraw foreground
      if( selectedScreen()==scnHome )
        displayHomeScreen();
      else
        displayMenuScreen();

  }; // message.command != cmdBoilerSending
};

void Display::displayHomeScreen() {
  TFT_eSprite sprite = TFT_eSprite(tft);
  const int BUFLEN = 80;
  char buffer[BUFLEN];

  if ( selectedScreen()==scnHome ) {
    Serial.println("Display::displayHomeScreen()");

    time_t now;
    time(&now); // Get current UTC time
    struct tm * localTime;
    localTime = localtime(&now); // Convert UTC to local time

    // Display date on top of screen
    const int W=292;
    const int H=30;
    sprite.createSprite(W, H);
    sprite.fillSprite(CLR_BACKGROUND);
    sprite.setTextDatum(MC_DATUM);
    sprite.loadFont(FONT_DATE, LittleFS);

    sprite.setTextColor(CLR_DARK_TEXT, CLR_BACKGROUND);
    strftime(buffer, BUFLEN, "%A %e %B", localTime);
    sprite.drawString(buffer, W/2, H/2);
    sprite.pushSprite(0, 0);
    sprite.unloadFont();
    sprite.deleteSprite();

    // Display time
    sprite.createSprite(80, 32);
    sprite.fillSprite(CLR_BACKGROUND);
    sprite.setTextDatum(MC_DATUM);
    sprite.loadFont(FONT_TIME, LittleFS);
    sprite.setTextColor(CLR_DARK_TEXT, CLR_CIRCLE_FILL);
    strftime(buffer, BUFLEN, "%R", localTime);
    sprite.drawString(buffer, 40, 16);
    sprite.pushSprite(118, 42);
    sprite.unloadFont();
    sprite.deleteSprite();

    // Display temperature setpoint
    sprite.createSprite(56, 32);
    sprite.fillSprite(CLR_BACKGROUND);
    // sprite.loadFont(FONT_TIME);
    sprite.loadFont(FONT_TIME, LittleFS);

    sprite.setTextDatum(MR_DATUM);
    sprite.setTextColor(controllerData->overrideTempNow ? CLR_RED_TEXT : CLR_DARK_TEXT, CLR_BACKGROUND);
    snprintf(buffer, BUFLEN, "%.1f", controllerData->temperatureSetpoint );
    sprite.drawString(buffer, 55, 16);
    sprite.pushSprite(137, 147);
    sprite.unloadFont();
    sprite.deleteSprite();

    // Display measured temperature
    sprite.createSprite(116, 64);
    sprite.fillSprite(CLR_BACKGROUND);
    // sprite.loadFont(FONT_TEMP_MEASURED);
    sprite.loadFont(FONT_TEMP_MEASURED, LittleFS);
    sprite.setTextDatum(MR_DATUM);
    sprite.setTextColor(CLR_MEASURED_TEMP, CLR_BACKGROUND);
    snprintf(buffer, BUFLEN, "%.1f", controllerData->measuredTemperature() );
    sprite.drawString(buffer, 115, 32);
    sprite.pushSprite(100, 79);
    sprite.unloadFont();
    sprite.deleteSprite();

    // Icons
    drawJpeg(tft, ICONS[controllerData->dspWifiIcon  ].c_str(), 6,  42);
    drawJpeg(tft, ICONS[controllerData->dspBoilerIcon].c_str(), 6,  78);
    drawJpeg(tft, ICONS[controllerData->dspFlameIcon ].c_str(), 6, 114);
    drawJpeg(tft, ICONS[controllerData->dspShowerIcon].c_str(), 6, 150);

    // Day icons
    int x=0;
    for(int i=0; i<7; i++) {
      if( controllerData->dayTypeOverruled[i] ) {
        tft->fillSmoothRoundRect( x , 194, 42, 42, 8, CLR_RED_TEXT,   CLR_BACKGROUND);
        tft->fillSmoothRoundRect(x+2, 196, 38, 38, 6, CLR_BACKGROUND, CLR_RED_TEXT  );
      }
      drawJpeg(tft, ICONS[ DAYTYPE_TO_ICON[ controllerData->dayTypes[i] ] ].c_str(), x+5, 199);
      x+=40;
    }
  };
};

void Display::displayMenuScreen() {
  TFT_eSprite sprite = TFT_eSprite(tft);

  int showSubMenuLines=0;
  char subMenuLine1[MAX_LENGTH_SUBMENU];
  char subMenuLine2[MAX_LENGTH_SUBMENU];
  struct tm * timeinfo;
  time_t now;
  char buffer[32];

  Serial.printf("Display::displayMenuScreen() %s > %s\n", screenTitle[selectedScreen()].c_str(), commandLabels[selectedMenuItem()].c_str() );

  // Determine which subtitles to display
  switch( selectedScreen() ) {

    case scnOverruleMultiple:
      if( controllerData->multipleForever) {
        showSubMenuLines = 1;
        snprintf(subMenuLine1, MAX_LENGTH_SUBMENU, "%s forever", DAY_TYPES[controllerData->overrideMultiple].c_str() );
      }
      else {
        showSubMenuLines = 2;

        snprintf(subMenuLine1, MAX_LENGTH_SUBMENU, "%s for %d days", DAY_TYPES[controllerData->overrideMultiple].c_str(), controllerData->overrideMultipleCount);

        time(&now);                    // Get current UTC time
        timeinfo = localtime(&now);    // Get local time
        timeinfo->tm_mday += controllerData->overrideMultipleCount-1; // controllerData->overrideMultipleCount = 1 means today
        mktime(timeinfo);
        strftime(buffer, 32, "%A %e %B", timeinfo);
        snprintf( subMenuLine2, MAX_LENGTH_SUBMENU, "last day is %s", buffer);
      }
      break;

    case scnSettingsTemperature:
      showSubMenuLines = 2;
      snprintf( subMenuLine1, MAX_LENGTH_SUBMENU, "High temperature %.1f°C", controllerData->highTemp);
      snprintf( subMenuLine2, MAX_LENGTH_SUBMENU, "Low temperature %.1f°C",  controllerData->lowTemp);
      break;

    case scnSettingsSensorOffset:
      showSubMenuLines = 2;
      snprintf( subMenuLine1, MAX_LENGTH_SUBMENU, "Sensor offset %.1f°C", controllerData->sensorOffset);
      snprintf( subMenuLine2, MAX_LENGTH_SUBMENU, "Measured temperature %.1f°C",  controllerData->measuredTemperature() );
      break;

    case scnSettingsHomeTimes:
      showSubMenuLines=1;
      snprintf( subMenuLine1, MAX_LENGTH_SUBMENU, "Wake up %s sleep %s", controllerData->workFromHomeWakeUp.str().c_str(), controllerData->workFromHomeSleep.str().c_str() );
      break;

    case scnSettingsOfficeTimes:
      showSubMenuLines=2;
      snprintf( subMenuLine1, MAX_LENGTH_SUBMENU, "Wake up %s go out %s",  controllerData->workAtOfficeWakeUp.str().c_str(), controllerData->workAtOfficeGoOut.str().c_str() );
      snprintf( subMenuLine2, MAX_LENGTH_SUBMENU, "come home %s sleep %s", controllerData->workAtOfficeComeIn.str().c_str(), controllerData->workAtOfficeSleep.str().c_str() );
      break;

    case scnSettingsWeekendTimes:
      showSubMenuLines=1;
      snprintf( subMenuLine1, MAX_LENGTH_SUBMENU, "Wake up %s sleep %s", controllerData->weekendWakeUp.str().c_str(), controllerData->weekendSleep.str().c_str() );
      break;

    default:
      showSubMenuLines = 0;
  }

  sprite.createSprite(320, 24);

  // Draw the titles to display
  sprite.fillSprite(CLR_BACKGROUND);
  sprite.setTextColor(CLR_MENU_TITLE, CLR_BACKGROUND);
  // sprite.loadFont(FONT_MENU_HEADER);
  sprite.loadFont(FONT_MENU_HEADER, LittleFS);

  sprite.setTextDatum(TL_DATUM);
  sprite.drawString(screenTitle[selectedScreen()].c_str(), 2, 2);
  sprite.pushSprite(0, 0);

  int y=sprite.height()+4;

  if(showSubMenuLines>0) {
    sprite.fillSprite(CLR_BACKGROUND);
    // sprite.loadFont(FONT_SUBMENU);
    sprite.loadFont(FONT_SUBMENU, LittleFS);

    sprite.setTextColor(CLR_MENU_SUBTITLE, CLR_BACKGROUND);
    sprite.drawString(subMenuLine1, 2, 0);
    sprite.pushSprite(0, y);
    y+=sprite.height();
  };

  if(showSubMenuLines>1) {
    sprite.fillSprite(CLR_BACKGROUND);
    sprite.drawString(subMenuLine2, 2, 0);
    sprite.pushSprite(0, y);
    y+=sprite.height();
  };

  // sprite.loadFont(FONT_SUBMENU);
  sprite.loadFont(FONT_SUBMENU, LittleFS);

  int newH = sprite.fontHeight()+4;

  sprite.unloadFont();
  sprite.deleteSprite();

  sprite.createSprite(320, newH);
  // sprite.loadFont(FONT_SUBMENU);
  sprite.loadFont(FONT_SUBMENU, LittleFS);


  // Determine if the menu needs to scroll up
  int y2 = y;
  int firstItem=0;
  for (auto& menuItem : SCREENS[selectedScreen()] ) {
    y2+=sprite.height();
    if(y2>240) firstItem++;
    if(menuItem==selectedMenuItem()) {
      break;
    }
  }

  int itemNr=0;
  for (auto& menuItem : SCREENS[selectedScreen()] ) {

    if(itemNr>=firstItem) {
      sprite.fillSprite(CLR_BACKGROUND);
      if(menuItem==selectedMenuItem()) {
        sprite.setTextColor(CLR_MENU_SELECT, CLR_BACKGROUND);
        sprite.drawString(">", 0, 2);
      }
      else
        sprite.setTextColor(CLR_MENU_TEXT, CLR_BACKGROUND);

      sprite.drawString(commandLabels[menuItem].c_str(), 12, 2);
      sprite.pushSprite(0, y);
      y+=sprite.height();
    }
    itemNr++;
  }

  sprite.unloadFont();
  sprite.deleteSprite();
};

/******************************************
 * GLOBAL VARIABLES                       *
 ******************************************/
TFT_eSPI tft = TFT_eSPI();  // Driver for display
Display display(tft, controllerData, &selectedScreen, &selectedMenuItem); // Display

void checkDisplayQueue() {
  userEventMessage_t message;
  userEventMessage_t messageOut;

  if( xQueueReceive( displayQueue, &message, 0) == pdPASS ) {

    Serial.printf("%s > Display [%s] k=%d\n", senderLabels[message.sender].c_str(), commandLabels[message.command].c_str(), keyboardEnabed );

    disableKeyboard(); // Disable keyboard so display can use SPI
    display.processMessage(message);
    enableKeyboard();  // Enable keyboard again

    switch( message.command ) {

      case cmdBoilerSending:
        messageOut = userEventMessage_t();
        sendMessage(sndDisplay, cmdBoilerSending, temperatureQueue);
        break;

      case cmdUpdateScreen:
        // Switch on the backlight
        sendMessage(sndDisplay, cmdBacklightOn, backlightQueue); // Switch on backlight
        break;

    } // switch
  } // xQueueReceive
}


// Start the the display handler
void startDisplay() {
  display.start();
}
