henkjannl/RoomThermostat/05 Software/Roomthermostat V2/Roomthermostat V2.0/src/j_jpeg.h

#pragma once

#define LOAD_FLASH_FS

#include <TFT_eSPI.h>
#include <JPEGDecoder.h>

/*====================================================================================
  This sketch contains support functions to render the Jpeg images.

  Created by Bodmer 15th Jan 2017
  Updated by Bodmer to support ESP32 with SPIFFS Jan 2018
  ==================================================================================*/

// Return the minimum of two values a and b
#define minimum(a,b)     (((a) < (b)) ? (a) : (b))

//====================================================================================
//   Decode and render the Jpeg image onto the TFT screen
//====================================================================================
void jpegRender(TFT_eSPI *tft, int xpos, int ypos) {

  // retrieve information about the image
  uint16_t  *pImg;
  int16_t mcu_w = JpegDec.MCUWidth;
  int16_t mcu_h = JpegDec.MCUHeight;
  int32_t max_x = JpegDec.width;
  int32_t max_y = JpegDec.height;

  // Jpeg images are draw as a set of image block (tiles) called Minimum Coding Units (MCUs)
  // Typically these MCUs are 16x16 pixel blocks
  // Determine the width and height of the right and bottom edge image blocks
  int32_t min_w = minimum(mcu_w, max_x % mcu_w);
  int32_t min_h = minimum(mcu_h, max_y % mcu_h);

  // save the current image block size
  int32_t win_w = mcu_w;
  int32_t win_h = mcu_h;

  // record the current time so we can measure how long it takes to draw an image
  uint32_t drawTime = millis();

  // save the coordinate of the right and bottom edges to assist image cropping
  // to the screen size
  max_x += xpos;
  max_y += ypos;

  // read each MCU block until there are no more
  while ( JpegDec.readSwappedBytes()) { // Swapped byte order read

    // save a pointer to the image block
    pImg = JpegDec.pImage;

    // calculate where the image block should be drawn on the screen
    int mcu_x = JpegDec.MCUx * mcu_w + xpos;  // Calculate coordinates of top left corner of current MCU
    int mcu_y = JpegDec.MCUy * mcu_h + ypos;

    // check if the image block size needs to be changed for the right edge
    if (mcu_x + mcu_w <= max_x) win_w = mcu_w;
    else win_w = min_w;

    // check if the image block size needs to be changed for the bottom edge
    if (mcu_y + mcu_h <= max_y) win_h = mcu_h;
    else win_h = min_h;

    // copy pixels into a contiguous block
    if (win_w != mcu_w)
    {
      for (int h = 1; h < win_h-1; h++)
      {
        memcpy(pImg + h * win_w, pImg + (h + 1) * mcu_w, win_w << 1);
      }
    }

    // draw image MCU block only if it will fit on the screen
    if ( mcu_x < tft->width() && mcu_y < tft->height())
    {
      // Now push the image block to the screen
      tft->pushImage(mcu_x, mcu_y, win_w, win_h, pImg);
    }

    else if ( ( mcu_y + win_h) >= tft->height()) JpegDec.abort();

  }

  // calculate how long it took to draw the image
  drawTime = millis() - drawTime; // Calculate the time it took
}

//====================================================================================
//   Opens the image file and prime the Jpeg decoder
//====================================================================================
void drawJpeg(TFT_eSPI *tft, const char *filename, int xpos, int ypos) {

  // Open the named file (the Jpeg decoder library will close it after rendering image)
  //  File jpegFile = SD.open( filename, FILE_READ);  // or, file handle reference for SD library
  // fs::File jpegFile = SPIFFS.open( filename, "r");    // File handle reference for SPIFFS
  fs::File jpegFile = LittleFS.open(filename, "r");

  //ESP32 always seems to return 1 for jpegFile so this null trap does not work
  if ( !jpegFile ) {
    Serial.print("drawJpeg ERROR: File \""); Serial.print(filename); Serial.println ("\" not found!");
    return;
  }

  // Use one of the three following methods to initialise the decoder,
  // the filename can be a String or character array type:

  //boolean decoded = JpegDec.decodeFsFile(jpegFile); // Pass a SPIFFS file handle to the decoder,
  //boolean decoded = JpegDec.decodeSdFile(jpegFile); // or pass the SD file handle to the decoder,
  boolean decoded = JpegDec.decodeFsFile(filename);  // or pass the filename (leading / distinguishes SPIFFS files)

  if (decoded) {
    // render the image onto the screen at given coordinates
    jpegRender(tft, xpos, ypos);
  }
  else {
    Serial.print("drawJpeg ERROR: File \""); Serial.print(filename); Serial.println ("\" Jpeg file format not supported");
  }
}
