henkjannl/RoomThermostat/05 Software/Tests/Test20_fileServer/Test20_fileServer.ino

/*
  upload the contents of the data folder with MkSPIFFS Tool ("ESP32 Sketch Data Upload" in Tools menu in Arduino IDE)
  or you can upload the contents of a folder if you CD in that folder and run the following command:
  for file in `ls -A1`; do curl -F "file=@$PWD/$file" esp32fs.local/edit; done

  access the sample web page at http://esp32fs.local
  edit the page by going to http://esp32fs.local/edit
*/
#include <WiFi.h>
#include <WiFiClient.h>
#include <WebServer.h>
#include <ESPmDNS.h>
#include "MyCredentials.h"

// You only need to format the SPIFFS once
#include <SPIFFS.h>

WebServer server(80);
//holds the current upload
//File fsUploadFile;

/*
//format bytes
String formatBytes(size_t bytes) {
  if (bytes < 1024) {
    return String(bytes) + "B";
  } else if (bytes < (1024 * 1024)) {
    return String(bytes / 1024.0) + "KB";
  } else if (bytes < (1024 * 1024 * 1024)) {
    return String(bytes / 1024.0 / 1024.0) + "MB";
  } else {
    return String(bytes / 1024.0 / 1024.0 / 1024.0) + "GB";
  }
}
*/

String getContentType(String filename) {
  if (server.hasArg("download")) {
    return "application/octet-stream";
  } else if (filename.endsWith(".htm")) {
    return "text/html";
  } else if (filename.endsWith(".html")) {
    return "text/html";
  } else if (filename.endsWith(".css")) {
    return "text/css";
  } else if (filename.endsWith(".js")) {
    return "application/javascript";
  } else if (filename.endsWith(".png")) {
    return "image/png";
  } else if (filename.endsWith(".gif")) {
    return "image/gif";
  } else if (filename.endsWith(".jpg")) {
    return "image/jpeg";
  } else if (filename.endsWith(".ico")) {
    return "image/x-icon";
  } else if (filename.endsWith(".xml")) {
    return "text/xml";
  } else if (filename.endsWith(".pdf")) {
    return "application/x-pdf";
  } else if (filename.endsWith(".zip")) {
    return "application/x-zip";
  } else if (filename.endsWith(".gz")) {
    return "application/x-gzip";
  }
  return "text/plain";
}

bool exists(String path){
  bool yes = false;
  File file = SPIFFS.open(path, "r");
  if(!file.isDirectory()){
    yes = true;
  }
  file.close();
  return yes;
}

bool handleFileRead(String path) {
  Serial.println("handleFileRead: " + path);
  if (path.endsWith("/")) {
    path += "index.htm";
  }
  String contentType = getContentType(path);
  String pathWithGz = path + ".gz";
  if (exists(pathWithGz) || exists(path)) {
    if (exists(pathWithGz)) {
      path += ".gz";
    }
    File file = SPIFFS.open(path, "r");
    server.streamFile(file, contentType);
    file.close();
    return true;
  }
  return false;
}

/*
void handleFileUpload() {
  if (server.uri() != "/edit") {
    return;
  }
  HTTPUpload& upload = server.upload();
  if (upload.status == UPLOAD_FILE_START) {
    String filename = upload.filename;
    if (!filename.startsWith("/")) {
      filename = "/" + filename;
    }
    Serial.print("handleFileUpload Name: "); Serial.println(filename);
    fsUploadFile = SPIFFS.open(filename, "w");
    filename = String();
  } else if (upload.status == UPLOAD_FILE_WRITE) {
    //Serial.print("handleFileUpload Data: "); Serial.println(upload.currentSize);
    if (fsUploadFile) {
      fsUploadFile.write(upload.buf, upload.currentSize);
    }
  } else if (upload.status == UPLOAD_FILE_END) {
    if (fsUploadFile) {
      fsUploadFile.close();
    }
    Serial.print("handleFileUpload Size: "); Serial.println(upload.totalSize);
  }
}

void handleFileDelete() {
  if (server.args() == 0) {
    return server.send(500, "text/plain", "BAD ARGS");
  }
  String path = server.arg(0);
  Serial.println("handleFileDelete: " + path);
  if (path == "/") {
    return server.send(500, "text/plain", "BAD PATH");
  }
  if (!exists(path)) {
    return server.send(404, "text/plain", "FileNotFound");
  }
  SPIFFS.remove(path);
  server.send(200, "text/plain", "");
  path = String();
}

void handleFileCreate() {
  if (server.args() == 0) {
    return server.send(500, "text/plain", "BAD ARGS");
  }
  String path = server.arg(0);
  Serial.println("handleFileCreate: " + path);
  if (path == "/") {
    return server.send(500, "text/plain", "BAD PATH");
  }
  if (exists(path)) {
    return server.send(500, "text/plain", "FILE EXISTS");
  }
  File file = SPIFFS.open(path, "w");
  if (file) {
    file.close();
  } else {
    return server.send(500, "text/plain", "CREATE FAILED");
  }
  server.send(200, "text/plain", "");
  path = String();
}

void handleFileList() {
  if (!server.hasArg("dir")) {
    server.send(500, "text/plain", "BAD ARGS");
    return;
  }

  String path = server.arg("dir");
  Serial.println("handleFileList: " + path);


  File root = SPIFFS.open(path);
  path = String();

  String output = "[";
  if(root.isDirectory()){
      File file = root.openNextFile();
      while(file){
          if (output != "[") {
            output += ',';
          }
          output += "{\"type\":\"";
          output += (file.isDirectory()) ? "dir" : "file";
          output += "\",\"name\":\"";
          output += String(file.name()).substring(1);
          output += "\"}";
          file = root.openNextFile();
      }
  }
  output += "]";
  server.send(200, "text/json", output);
}
*/

void setup(void) {
  Serial.begin(115200);
  Serial.print("\n");
  Serial.setDebugOutput(true);
  SPIFFS.begin();
  {
      File root = SPIFFS.open("/");
      File file = root.openNextFile();
      while(file){
          String fileName = file.name();
          size_t fileSize = file.size();
//          Serial.printf("FS File: %s, size: %s\n", fileName.c_str(), formatBytes(fileSize).c_str());
          file = root.openNextFile();
      }
      Serial.printf("\n");
  }


  //WIFI INIT
  Serial.printf("Connecting to %s\n", ssid);
  if (String(WiFi.SSID()) != String(ssid)) {
    WiFi.mode(WIFI_STA);
    WiFi.begin(ssid, password);
  }

  while (WiFi.status() != WL_CONNECTED) {
    delay(500);
    Serial.print(".");
  }
  Serial.println("");
  Serial.print("Connected! IP address: ");
  Serial.println(WiFi.localIP());

  MDNS.begin(host);
  Serial.print("Open http://");
  Serial.print(host);
  Serial.println(".local/edit to see the file browser");


  //SERVER INIT
  
  //load editor
  server.on("/edit", HTTP_GET, []() {
    if (!handleFileRead("/edit.htm")) {
      server.send(404, "text/plain", "FileNotFound");
    }
  });


  //called when the url is not defined here
  //use it to load content from SPIFFS
  server.onNotFound([]() {
    if (!handleFileRead(server.uri())) {
      server.send(404, "text/plain", "FileNotFound");
    }
  });


}

void loop(void) {
  server.handleClient();
  delay(200);//allow the cpu to switch to other tasks
}
